Mala2/MouDio/Documentation/BT-806/Drivers/ReadMe.txt

CP210x.zip:
CP210x Windows Driver For BP109, DB101, DB102, DB005, DB006, etc
