Mala2/MouDio/Prototype/Old Version/README.md

# Bluetooth-Speaker
<p align="center">
**⚠  This project is currently still under development. If you came from Reddit just wait I will organize the files soon ⚠️**
	
Discord https://discord.gg/edw5AbDd
<p align="center">
     

</p>
<p align="center">
	<a href="https://github.com/Mala2/Bluetooth-Speaker/repo-size" alt="repo-size">
		</a>
	<a href="https://github.com/Mala2/Bluetooth-Speaker/issues" alt="Issues">
		</a>
	<a href="https://github.com/sparkfun/Qwiic_SerLCD_Py/blob/master/LICENSE" alt="License">
		</a> 
 	<a href="https://discord.gg/GqjnZJyF" alt="Issues">
		</a>
	<a href="https://twitter.com/intent/follow?screen_name=Electricshocksa">
        	</a>
	<a href="https://twitter.com/intent/follow?screen_name=Muhammadalali">
        	</a>
	<a href="https://github.com/Mala2">
        	</a>
	<a href="https://github.com/Mala2/Bluetooth-Speaker/stargazers" alt="stars">
		</a>

A fully function Bluetooth Speaker implement most of the new ICs chip.

The design consists of four PCBs (MAIN, USB-C, FRONT, TOP) and 3 microcontrollers. I build and test all the PCBs and they work as expected so the hardware design is done. **However, the software part is still under process.**

Please refer to the shared files for more information about specific PCB.

🎨 📐 FUSION 360 (https://a360.co/3uLzq06)

[*🎨 📐 View on FUSION 360*](https://a360.co/3uLzq06)

Features
-------------------
* **Amplifier** - The Texas Instruments® **TPA3130D2** Which has low distrition can output 2 × 15 W Into a 8-Ω BTL Load
* **Connectivity** - The [*FSC-BT806 Feasycom*](https://github.com/Mala2/FSC-BT806) features 
 Qualcomm® **CSR8675** - **Bluetooth V5.0** Support HSP, HFP, A2DP, AVRCP, PBAP,MAP,SPP,BLE profile - Coverage up to 15m - **True Wireless Stereo** to share BT audio stream between two Speakers - **Wired** analog input
* **Power** - Accept **USB PD** Delivery **5 to 24V** - **Fast Charging** in 3 hours - **USB A** Capable of **15W-5V,3A** - **Low idle power** consumption - A**10-hour** battery life - **5000mAh** battery capacity

* **Arduino IDE Programmable Bluetooth-Speaker**

Repository Contents
-------------------

👩‍🚀 **[.STL Files ](STL-Files)** • The **Bluetooth-Speaker** components in STL format (probably what you are looking for to 3d print)

🔉 **[Hardware](Hardware)** • The internal PCBs files (Gerber, Schematic) 

💻 **[Software](Software)** • Codes and Libraries for use with the **Bluetooth-Speaker**

📄 **[Documentation](Documentation)** • Data sheets, other references

🎥 **[Video](Video)** • Demonstration videos of the final project

🎲 **[Prototype](Prototype)** • Evaluation board, Cases, etc...

To Do List
-------------------

🔴 **Minimize the use of microcontrollers as the esp32 can handle much of the work done by atmegas.**
	
🔴 **Battery efficiency is critical here so using every possible way to reduce the consumption is needed.**
	
🔴 **The front PCB can only display time. I wanted to display weather temperature too with the help of ESP32.**
