Mala2/MouDio/Prototype/Old Version/Hardware/Main/README.md

<p align="center">
**⚠  This PCB is currently still under development. ⚠️**
  
FRONT
-------------------

FRONT (https://d2t1xqejof9utc.cloudfront.net/screenshots/pics/406df0fcc6033955165331e439d0659e/large.png)

BACK
-------------------

BACK (https://d2t1xqejof9utc.cloudfront.net/screenshots/pics/797c76d72846c0377390deae2d0703cb/large.png)
