Mala2/MouDio/Prototype/Old Version/Hardware/Laser Cut/README.md

You can use any Acrylic you would like, but in this case I wanted to hide the LEDs from direct view. The manfucture **Tap Plastics®** has a cool way to accomplish that by applying a unique Acrylic created for this reason.

By using the below **Chemcast Black LED Acrylic** all the LEDs will be hidden away inside and only let the light to glow through. In the other hand it will apear opaque once the LEDs are off

Chemcast Black LED Acrylic
--------------
Chemcast Black LED Acrylic (https://www.tapplastics.com/product/plastics/cut_to_size_plastic/black_led_sheet/668)

[*Chemcast Black LED Acrylic*](https://www.tapplastics.com/product/plastics/cut_to_size_plastic/black_led_sheet/668) **X1** For the front panel done by laser cut
