Mala2/MouDio/Prototype/Old Version/Hardware/Main/Schematic_Main_V1.pdf

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
H I | I J | J K | K 11 | 22 | 33 | 44 | 55 | 66 | 77 | 88 | 99

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
TITLE:
Sheet_1 | REV: 1.0
Date: | 2021-03-11

Sheet: 1/1
Drawn By: mfm1500

### Company: Your Company

16MHz

X1

TCEPQR

SW1

4

1

2
35

5v+ out

ATMEGA328P-AU

U11

(PCINT19/OC2B/INT1)PD3

1
(PCINT20/XCK/T0)PD4

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
(PCINT6/XTAL1/TOSC1)PB6

7
(PCINT7/XTAL2/TOSC2)PB7

8
(PCINT21/OC0B/T1)PD5

9
(PCINT22/OC0A/AIN0)PD6 10
(PCINT23/AIN1)PD7 11
(PCINT0/CLKO/ICP1)PB0 12
(PCINT1/OC1A)PB1 13
(PCINT2/SS#/OC1B)PB2 14
(PCINT3/OC2A/MOSI)PB3 15
(PCINT4/MISO)PB4 16 | PB5(SCK/PCINT5) 17 AVCC 18 ADC6 19 AREF 20 GND 21 ADC7 22 PC0(ADC0/PCINT8) 23 PC1(ADC1/PCINT9) 24 PC2(ADC2/PCINT10) 25 PC3(ADC3/PCINT11) 26 PC4(ADC4/SDA/PCINT12) 27 PC5(ADC5/SCL/PCINT13) 28 PC6(RESET#/PCINT14) 29 PD0(RXD/PCINT16) 30 PD1(TXD/PCINT17) 31 PD2(INT0/PCINT18) 32

A0_1

A1_1

A2_1

A3_1

A4_1

A5_1

RX_1

TX_1

D3_1 | D2_1
D4_1

D5_1
D6_1
D7_1
D8_1
D9_1
D10_1
D11_1
D12_1 | D13_1

22pF

C36

22pF

C37

## DTR_1 MICRO CONTROLLER

5v+ out | 5v+ out

## ATMEGA328

OUT_CH

LMBR120FT1G

D6

5v+ out

D11_1

GND

TX_1

RX_1
DTR_1

HDR-F-2.54_1x6

H2

1

2

3

4

5

6

5v+ out

rest_1

GND

GND

GND

100nF

C38

100nF

C39
100nF

C40 GND

GND

EN 5v

https://www.ti.com/tool/PMP9491

## VIN = 3V, VOUT = 12V,and IOUT = 2.5A

LM3481

## BOOST CONVERTER

https://www.ti.com/product/LM3481#design-development##all

LM3481MM/NOPB

U15

ISEN

1
UVLO

2
COMP

3
FB

4
AGND

5
FA/SYNC/SD

6

PGND

7

DR

8

VCC

9

VIN 10

470uF

C102
1uF

C103
1uF

C104

44.2k

XAL1010-332MEB

L10

1

2

MBRD835LT4G

D10

3

2

1

1uF

C105
1uF

C106

CSD16321Q5

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
R114

R115
100

3.32k

470nF

C112

## Vo=12V@2.5A

SJ

SJ7

2

1

GND

OUT_CH_1

GND

GND

GND

GND

GND

EN 12v

GND

Next time: you can use variable resistor controled with microcontrollers to set the gain "I2C protocol" https://www.ti.com/tool/PMP9491

RIN

LIN

4.7uF

C76

4.7uF

C77

RIN+

LIN+

4.7uF

C78
RIN-

LIN-

4.7uF

C79

TPA3130D2DAPR

U16

MODESEL

1
SDZ

2
FAULTZ

3
RINP

4
RINN

5
PLIMIT

6
GVDD

7
GAIN/SLV

8
GND

9
LINP 10
LINN 11
MUTE 12
AM2 13
AM1 14
AM0 15
SYNC 16 | AVCC 17 PVCC 18 PVCC 19 BSNL 20 OUTNL 21 GND 22 OUTPL 23 BSPL 24 GND 25 BSNR 26 OUTNR 27 GND 28 OUTPR 29 BSPR 30 PVCC 31 PVCC 32 EPAD ³³

PGND

SDZ

RIN+

LIN+

RIN-

LIN-

PLIM

R64
75K

47K

R63

1uF

C74

SGND

100K R61

SGND

4.7K

R62

47pF

C75

SGND

PGND | SGND

1000pF

C73
100nF

C71

PGND

BSNL

OUTNL

R69

10 PGND

10uH

L11

PGND
R68
3.32

PGND

J22
L-LN

R70
PGND

10uH

L12

PGND

R67

PGND

J21
L+
LP

OUTPL

BSPL

BSNR | PGND

R71

10uH

L13

PGND

R66

PGND

J20
R-RN

OUTNR

BSPR
OUTPR | PGND

R72

10

10

10

10uH

L14

PGND
PGND

R65

J19
R+
RP

1000pF

C72
100nF

C70

PGND

https://www.ti.com/product/TPA3130D2

## Amplifier TPA3130D2

3.32

3.32

3.32

GND

12V

D9_1

EN AMP

EN AMP

XH2.54-10P

J3

123456789

10

### XH2.54-10P

DATA_OUT

MUTE

MUTE

5V+

GND

OUT_CH

12V

5v+ out

A5_1 OUTLL

# GNDL

5V+

R

GND
5v+ out

OUTRR

1uF

C48
1uF

C43

A4_1

D7_1
D8_1

## SN74LVC1T45 LEVEL SHIFTER

GND

GND

100nF

C41

GND

100nF

C42

D5_1_LED_5V

SN74LVC1T45DBVT

U13

VCCA

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
VCCB

6

## SN74LVC1T45 LEVEL SHIFTER

GND

GND

100nF

C44

GND

100nF

C45

D6_1_LED_5V

SN74LVC1T45DBVT

U14

VCCA

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
VCCB

6

D5_1

D6_1

OUT_CH

OUT_CH | 5V+

5V+

D5_1_LED_5V
D6_1_LED_5V
LED+

A5_1
A4_1

HDR-F-2.54_1x2

H3 12

SDA

SCL

12V

Replace it with 10k as if digital used

LM5157

## Could be a good substitute for recent one

3.3 uH

R39 | 56.2K R40

2.2nF

C49
47nF

C50

R41

R42
56.2k

10pF

C51

R43
0.004

STAT

8.45K

R47

5V

RX_1
A3_1

5v+ out R L

GND-sound

A2541WR-7P

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
STAT

OUT_CH

DATA_OUT

5V

GND

OUT_CH

A2541WR-7P

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
TPS61235PRWLT

U1

PGND

1
SW

2
VIN

3
CC

4
AGND

5

FB

6

EN

7

INACT

8

VOUT

9

OUT_CH

GND
GND

GND

100nF

C21

GND

1M

R12
100nF

C24
34K

R13

## Boost Converter 5V 2A

22uF

C17

22uF

C18
22uF

C19
22uF
EN 5v | C20

1M

R1

332K
R2

5V+

D4_1 | EN BLE

FSC-BT806

IC1

GND_1

1

AIO0

2

AIO1

3

I2S_CLK

4

I2S_IN

5

I2S_OUT

6

I2S_WS

7

RESET

8

SPI_CSB

9

SPI_MOSI

10

SPI_MISO

11

SPI_CLK

12

BT_TX

13

BT_RX

14

BT_CTS

15

BT_RTS

16

LED0

17

LED1

18

LED2

19

PIO0

20

PIO1

21

GND_2

22

PIO2

23

PIO3

24

PIO4

25

PIO5

26

PIO6

27

PIO7

28

PIO14

29

PIO15

30

VDD_USB/3.3V_OUT

31

GND_3

32

VBAT_IN

33

VREGENABLE

34

1.8V_OUT

35

VDD_IO

36

USB_DP

37

USB_DN

38

VCC_CHG

39

MIC_RP

40

MIC_RN

41

MIC_R_BIAS

42

MIC_LP

43

MIC_LN

44

MIC_L_BIAS

45

SPK_RN

46

SPK_RP

47

SPK_LN

48

SPK_LP

49

GND_4

50

EXT_ANT

51

GND_5

52

GMI3015P-2C66DB

# MIC1¹²

GMI3015P-2C66DB

# MIC2¹²

MIC_L | MIC_R 15nH

L1
15nH

L2

15pF

C2
15pF

C3

GND_F | GND_F
GND_F | GND_F 100nF

C4
100nF

C5

100nF

C6
100nF

C7

2.2K

R6
2.2K

R7

MIC_RP

MIC_RN

MIC_L_P

MIC_L_N

MIC_BIAS_A | MIC_BIAS_B 0
MIC | R11

MIC/LINE_RN

MIC/LINE_RP

MIC/LINE_LN

MIC/LINE_LP

GND_F

SPK_L_P

SPK_L_N

SPK_R_P

SPK_R_N

MIC_BIAS_A

MIC/LINE_LN

MIC/LINE_LP

MIC_BIAS_B

MIC/LINE_RN

MIC/LINE_RP

USB_5V

1uF

C8

GND_F

3V3_MAIN

0

R15

1V8

0

R16

1uF

C9

GND_F

# VREG_IN³V³_MAIN

100nF

C10

4.7uF

C11

# GND_F ⁰

R17

2.2uF

C12

PIO15

PIO14

PIO7

PIO6

PIO5

PIO4

PIO3

PIO2

GND_F

PIO1

PIO0

LED2

LED1

LED0

BT_RTS

BT_CTS

BT_RX

BT_TX

SPI_CLK

SPI_MISO

SPI_MOSI

SPI_CSB

RESET

PCM-SYNC

PCM-OUT

PCM-IN

PCM-CLK

AIO1

AIO0

GND_F

BL9198-33BAPRN

U3

VIN

1
GND

2
EN
3 | NC

4

VOUT

5 | 3V3_MAIN

GND_F

100nF

C14
10pF

C15

GND_F

VBAT

## 3V3 regulator

NC

NC

NC

RESET

3V3_MAIN

100nF

C27

GND_F

3V3_MAIN

BT_RTS

NC

15K

R50

GND_F

100nF

C28

HDR-M-2.54_1x1

MUTE 1

## EN Pin(MUTE)

HDR-M-2.54_1x4

J1

k1
K2
K3
COM

VREG_IN

GND_F

POWER/PLAY/PAUSE
VOL+/NEXT
VOL-/BACK

K1: Long press for 2 seconds to Power On, short press to Pause K2: Long press to Volume+, short press to switch to Next Song K3: Long press to Volume-, short press to switch to Last Song

## Push Buttons

FC-B1010RGBT-HG

LED4

234

LED0

LED1
3V3_MAIN | LED2

## LED Indication

3V3_MAIN

PIO6
PIO7

## FSC-BT806B (CSR8675)

J4SD

J5
EN

EN: HIGH = ON

SD: LOW = ON

SDZ: HIGH = ON

PGND= POWER GND
SGND= SIGNAL GND
YOU SHOULD SEPARATE THEM NEAR THE DEVICE

XH2.54-4P

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
3V3_MAIN

LED11

LED22

LED00

LED11
LED22
LED00

Touch pad copy

D2

1

Touch pad copy

D3

1

Touch pad copy

A1

1

Touch pad copy

A0

1

A1_1

A0_1

## ATMEGA328 (Pinout)

12V

## (TPS61235P)

Jumper

JP2

GND

D2_1

D3_1

GND GND_F

JP4 Jumper

HDR-M-2.54_1x4

J7123

SPK_L_P

4

SPK_L_N

SPK_R_P

SPK_R_N

VBAT | OUT_CH

Touch pad copy

D4

1 D4_1

5017

U61 1

5017

U71 1

5017

1

U9

1

HDR-M-2.54_1x1

CH_B1 1

HDR-M-2.54_1x1

CH_A1
1

OUT_CH

MP3432

## 30W Boost Converter, VIN=2.7V

U10
1uH

L1

100uF

C34

C=0.22uF

2 | 15 W Into a 8- BTL Load at 15 V
Should be 10uF | https://ohmslawcalculator.com/voltage-divider-calculator
| DS1841

DS1841N+

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
RGND

6

RW

7

RH

8

NC

9

SCL 10

EP 11

OUT_CH_1
GND

OUT_CH

EN 12v

Touch pad copy

EN21

## AUDIO OUTPUT

SPK_R_N

SPK_L_N

SPK_R_P

SPK_L_P

MAX16054AZT+T

U2

IN

1
GND

2
CLEAR
3 | #OUT

4

OUT

5

VCC

6

## On/Off Controller MAX16054

5017

RN1 1

5017

LN

1 1

5017

1

RP

1

5017

LP

1 1

5.23K

R18

5.23K

R19

A5_1

A4_1

5v+ out

5v+ out

A5_1
A4_1

5v+ out

GND | 100nF C23

# GND RH

Jumper

JP1

RH

Touch pad copy

SDZ

1

D10_1

GND

IN
OUT_CH

Touch pad copy

O+

1

Touch pad copy

O-

1

O+
O-

O+

O-

HDR-F-2.54_1x2

H512

IN
GND

C0805X106J9RACTU

GMI6027P-2C-52db

MIC3

12

100nF

C26

1M

R14

1M

R20 | MAX4466 U4

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
10uF

C29

20K

R22
TC33X-2-104E

R23

100pF

C30

NFZ2MSM301SN10L

FB1

1

1
2

2

NFZ2MSM301SN10L

FB2

1

1
2

2

GND

5v+ out | 5v+ f

gnd f

gnd f
gnd f

gnd f

gnd f

5v+ f

5v+ f

5v+ f

out_AMP

220
R24

OUTRR

OUTLL

gnd f

270uF

C46
270uF

C47

MIC94041YFL-TR

U5

VOUT

1
GND

2
VIN

3

EN

4 EN 12v

2SK3541T2L

Q1

GND_F

1uF

C32 | VREG_IN

3V3_MAIN

HDR-F-2.54_1x2

H612

3V3_MAIN

GND_F

HDR-F-2.54_1x2

H712

OUT_CH

GND

HDR-F-2.54_1x2

H812

BT_TX
BT_RX

HDR-M-2.54_1x1

CH_B2 1

HDR-M-2.54_1x1

CH_B3 1

HDR-M-2.54_1x1

CH_B4 1

GND

GND

GND

GND

## Polypropylene (PP) film capacitors are best for audio

## AUDIO DETECTOR

Mouser Part #
80-R71XN447050H0K

Mouser Part #
80-R71XN447050H0K

80-R71XR510050H0K

OR

TPA3129D2 is better AMP

https://www.ti.com/lit/an/sloa201/sloa201.pdf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

LC FILTER

RC SNUBBER

You may need to add I2C breakout

667-ECW-FD2W475JB

OR

10nF

C52

OR
MKP2G021001C00JI00

Mouser Part #
GRM21BR72A103KA01L
C97925

10nF

C53

10nF

C55

10nF

C56

0.68uF

C57

Mouser Part #
GRM31MR71H684KA88L

ECW-F2684HAB

OR

0.68uF

C58

0.68uF

C59

0.68uF

C60

OR
MKP2F032201K00JSSD

Mouser Part #
810-C1608X7R1H224K

0.22uF

C61

0.22uF
C62

0.22uF

C63

0.22uF
C64

PGND

Mouser Part #
GRM1885C1H331JA01D

FKP2D003301D00JA00

OR

C85978

330pF

C65

330pF

C66

330pF

C67

330pF

C68

100uF

C1

100uF

C33
100uF

C16

200485-0710

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
GND_1

G1

GND_2

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
## TPS22969

## USE INSTEAD

TPS22969DNYT

U12

VIN_1

1

VIN_2

2

VBIAS

3

ON

4
GND

5

VOUT_1

6

VOUT_2

7

VOUT_3

8

VIN_3

9

## TPS22990

TPS22990

U17

CT

1
NC

2
VIN

3
VBIAS

4
ON
5 | GND

6

PG

7

VOUT

8

VOUT

9

VOUT

10

100K

R32 100K R33

100K

R25

100K

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
100K

R48

100K

R46

1K

R49

100uF

C22
100uF

C25

whiteLEDSMD

LED1

220
R28

220
R29

4.7uF

C13

270uF

C35

Mouser Part #
CLF12577NIT-100M-D

OR

1D23A-100M

SER2915L-332KL

U18

2

2
1

1
