Mala2/MouDio/Documentation/Pics/back 1.png

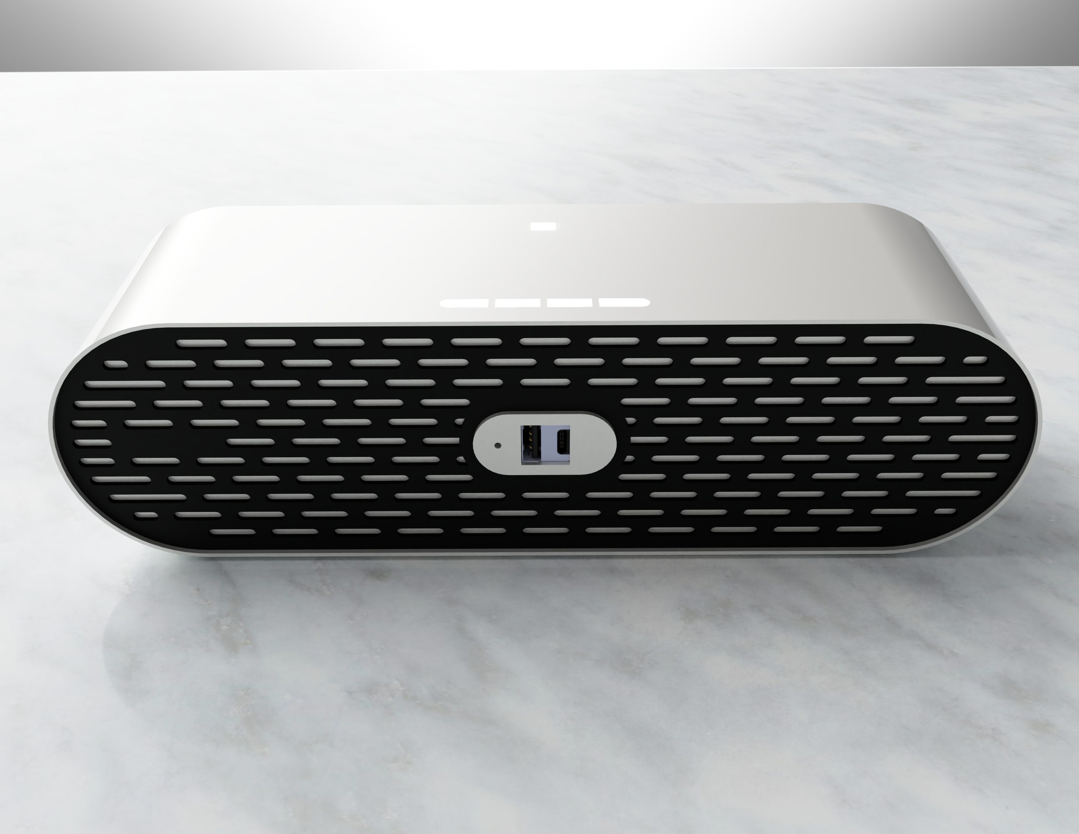
Documentation/Pics/back 1.png
