Mala2/MouDio/Documentation/Pics/back.png

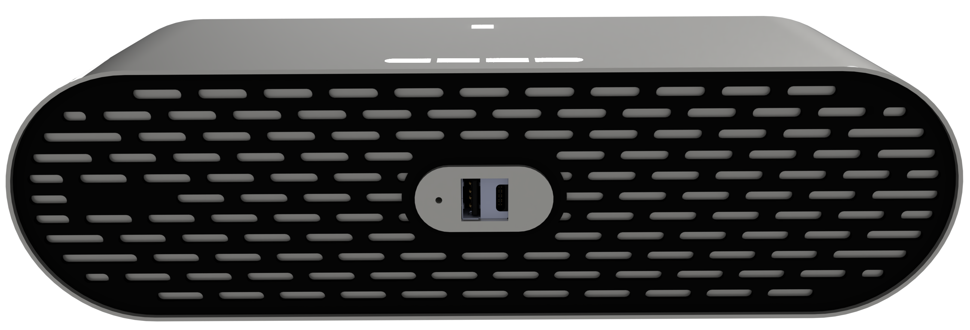
Documentation/Pics/back.png
