Mala2/MouDio/Documentation/Pics/BACK_Charger.png

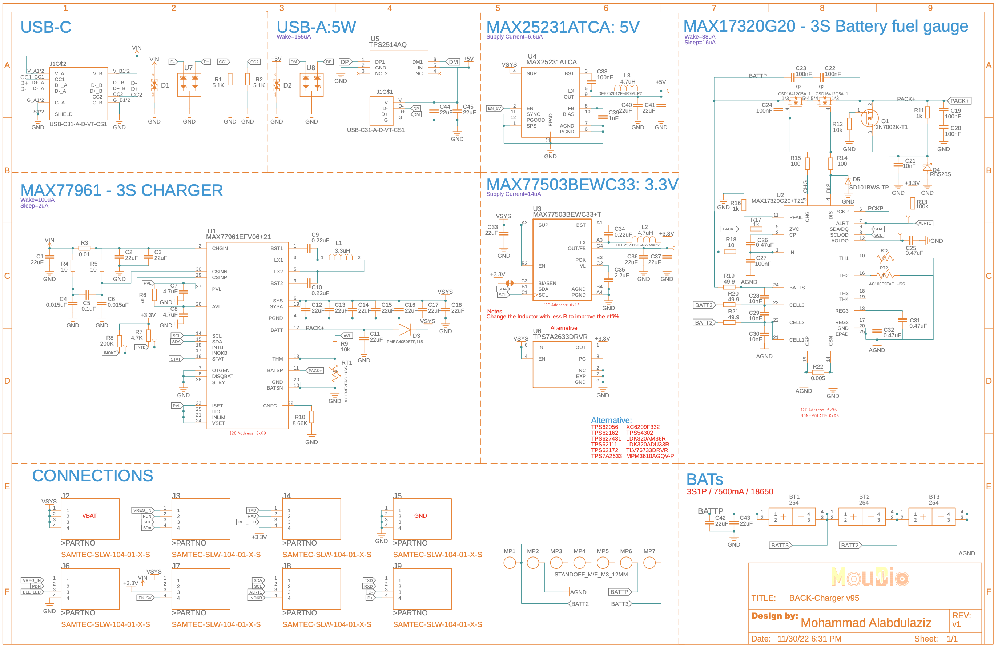
Documentation/Pics/BACK_Charger.png
