Mala2/MouDio/Documentation/Pics/BACK_Chargere_T.png

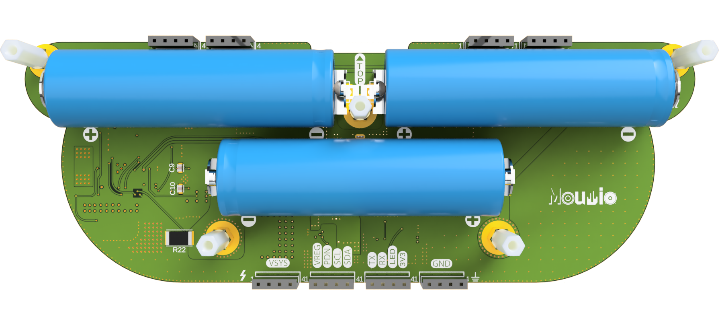
Documentation/Pics/BACK_Chargere_T.png
