Mala2/MouDio/Documentation/Pics/Battery Extension PCB Back V2.png

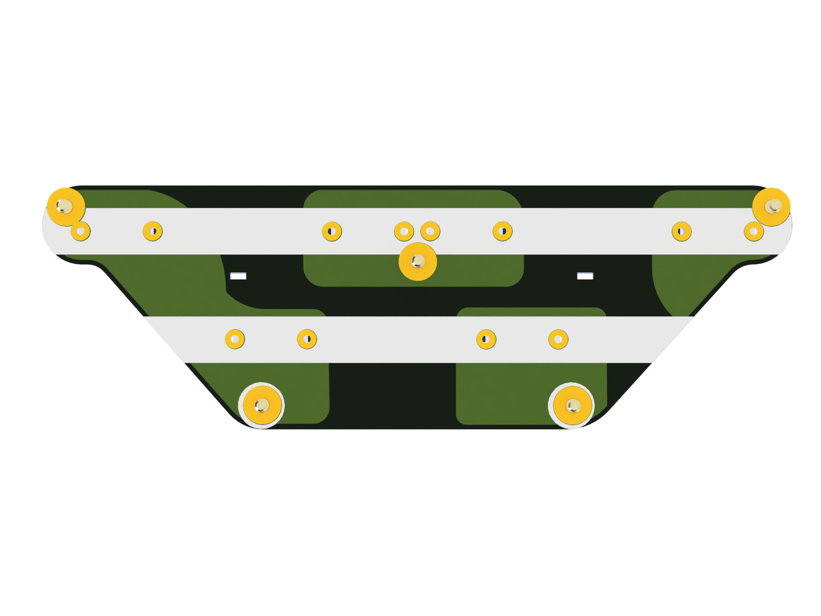
Documentation/Pics/Battery Extension PCB Back V2.png
