Mala2/MouDio/Documentation/Pics/Battery Extension PCB Front V2.png

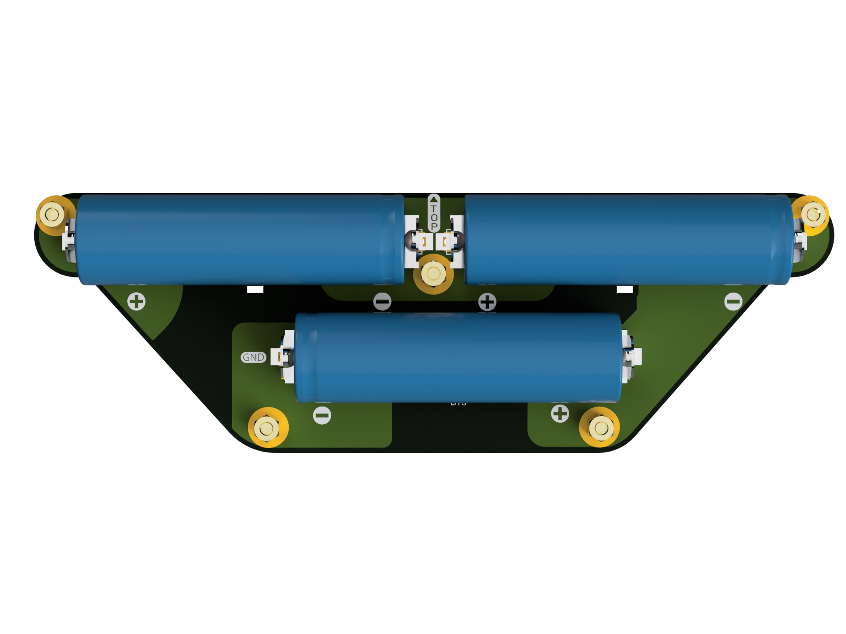
Documentation/Pics/Battery Extension PCB Front V2.png
