Mala2/MouDio/Documentation/Pics/BLUETOOTH SPEAKER 1.png

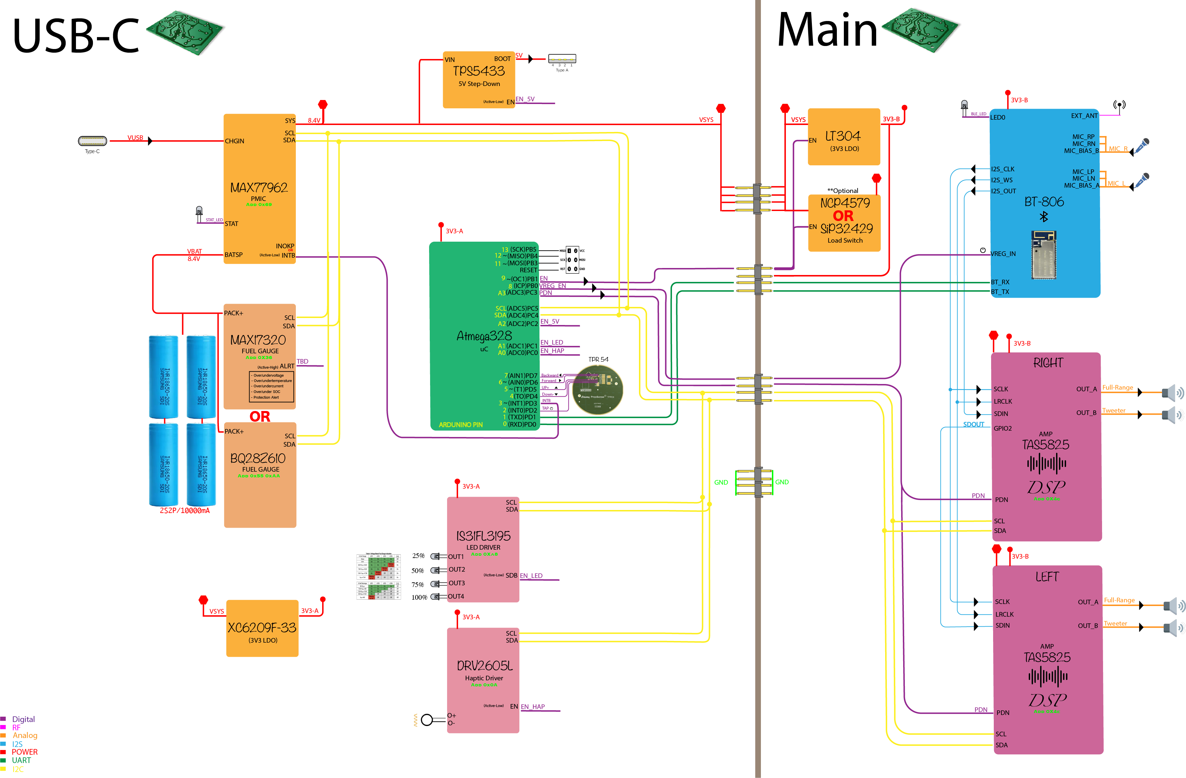
Documentation/Pics/BLUETOOTH SPEAKER 1.png
