Mala2/MouDio/Documentation/Pics/BOTTOM_Amplifier.png

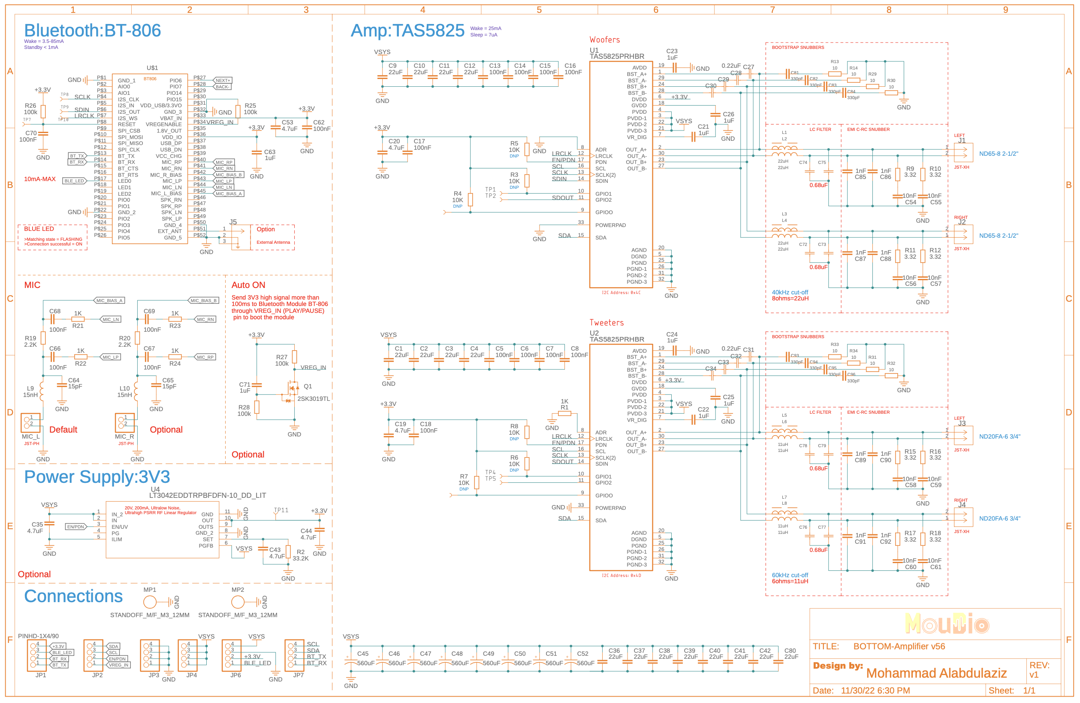
Documentation/Pics/BOTTOM_Amplifier.png
