Mala2/MouDio/Documentation/Pics/BOTTOM_Amplifier_B.png

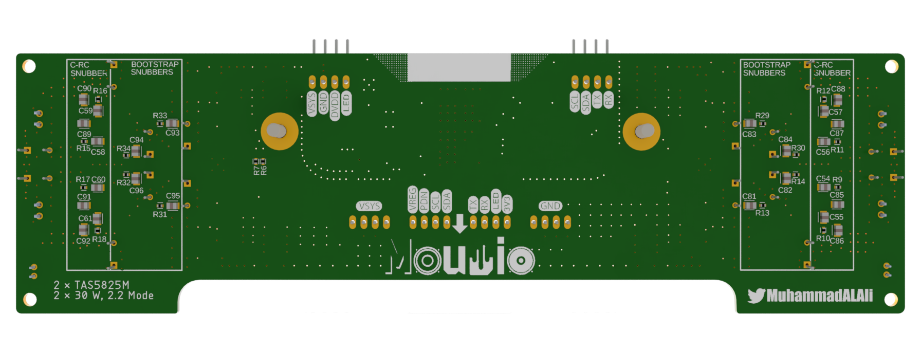
Documentation/Pics/BOTTOM_Amplifier_B.png
