Mala2/MouDio/Documentation/Pics/BOTTOM_Amplifier_T.png

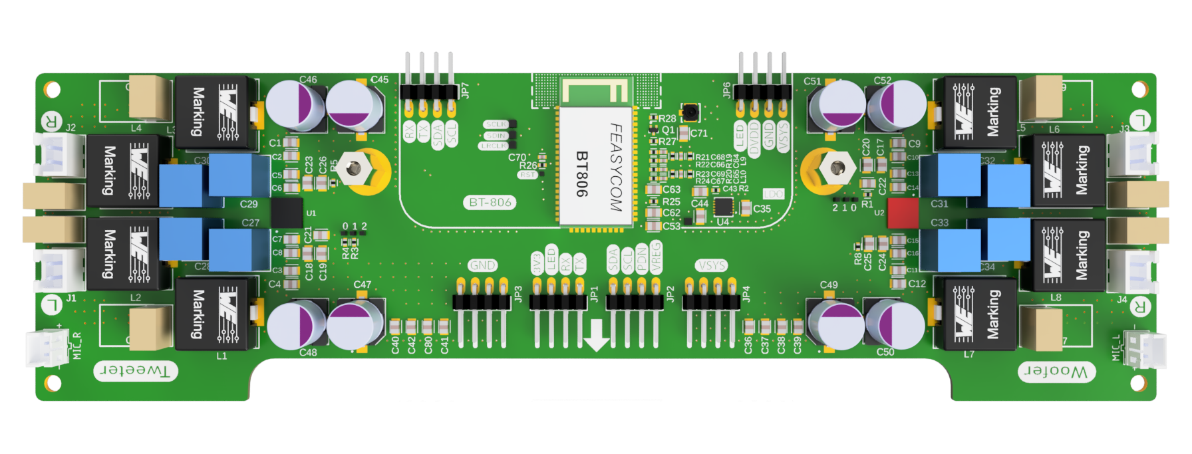
Documentation/Pics/BOTTOM_Amplifier_T.png
