Mala2/MouDio/Documentation/Pics/front angle.png

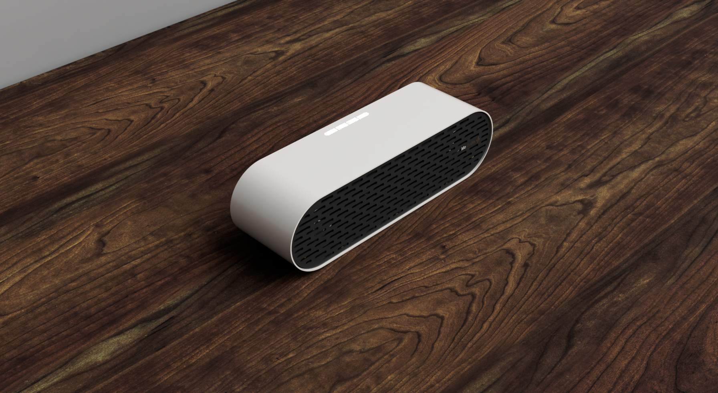
Documentation/Pics/front angle.png
