Mala2/MouDio/Documentation/Pics/front black.png

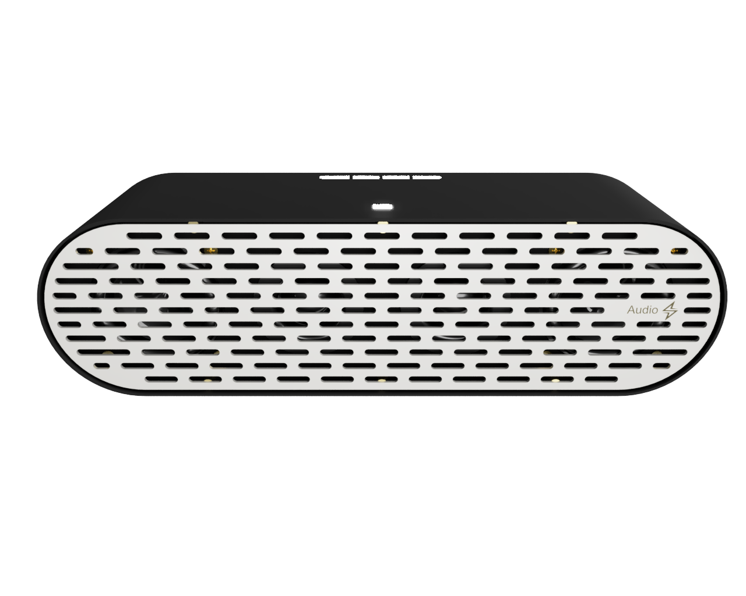
Documentation/Pics/front black.png
