Mala2/MouDio/Documentation/Pics/front cer.png

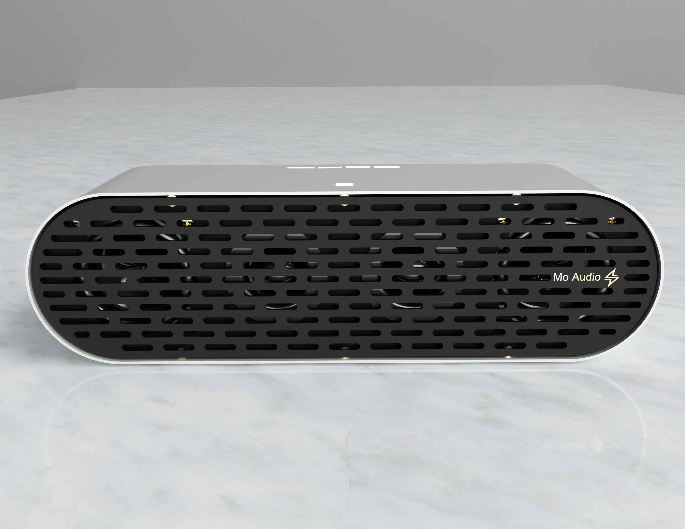
Documentation/Pics/front cer.png
