Mala2/MouDio/Documentation/Pics/front oreg.png

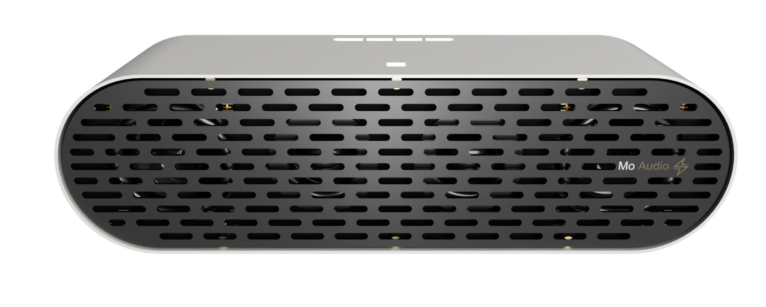
Documentation/Pics/front oreg.png
