Mala2/MouDio/Documentation/Pics/front wood.png

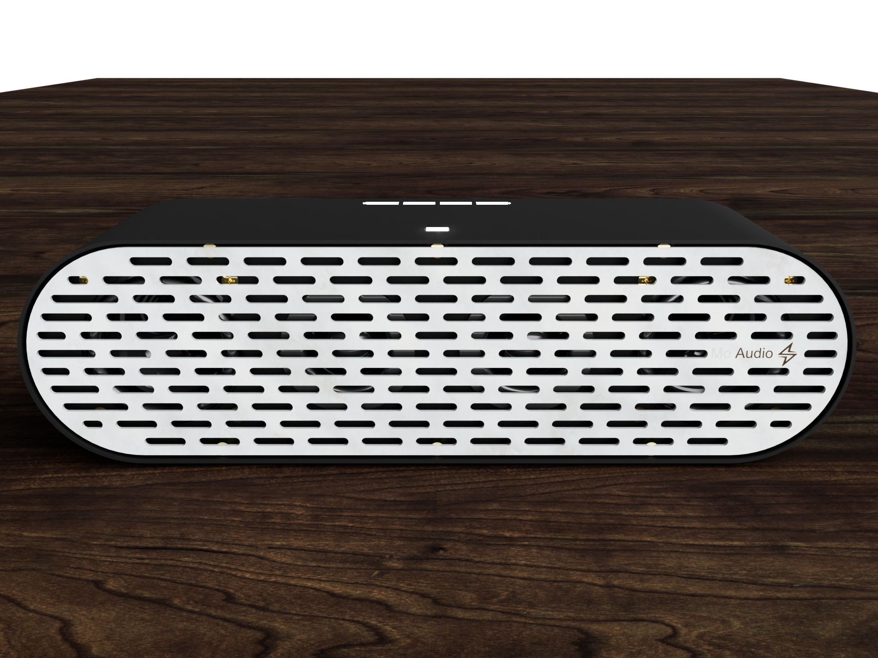
Documentation/Pics/front wood.png
