Mala2/MouDio/Documentation/Pics/front.png

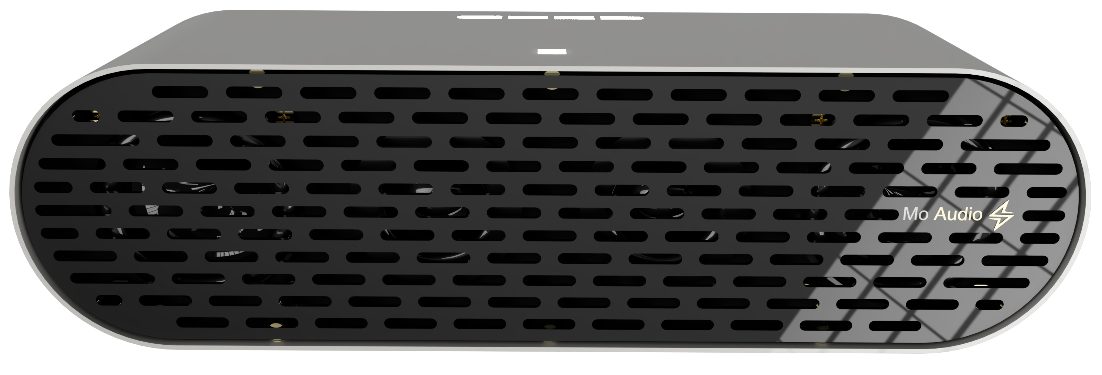
Documentation/Pics/front.png
