Mala2/MouDio/Documentation/Pics/FRONT_Speaker.png

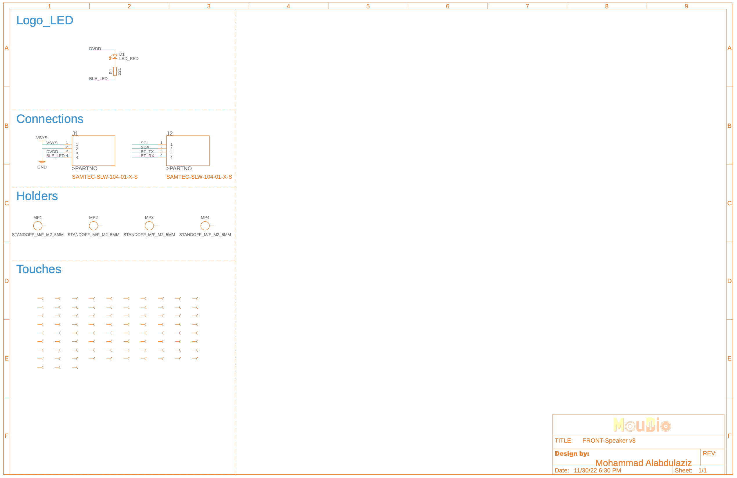
Documentation/Pics/FRONT_Speaker.png
