Mala2/MouDio/Documentation/Pics/Front_Speaker_B.png

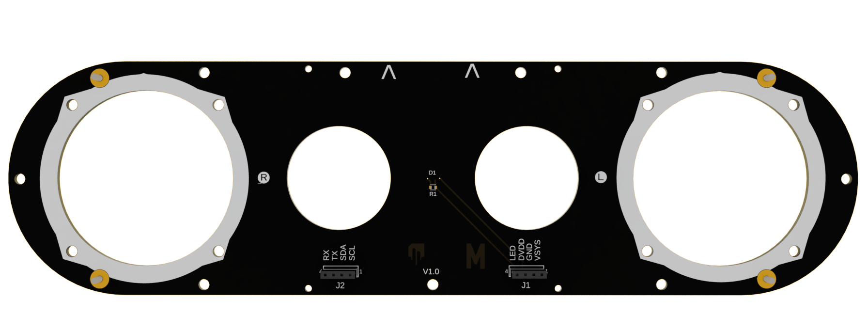
Documentation/Pics/Front_Speaker_B.png
