Mala2/MouDio/Documentation/Pics/FRONT_Speaker_T.png

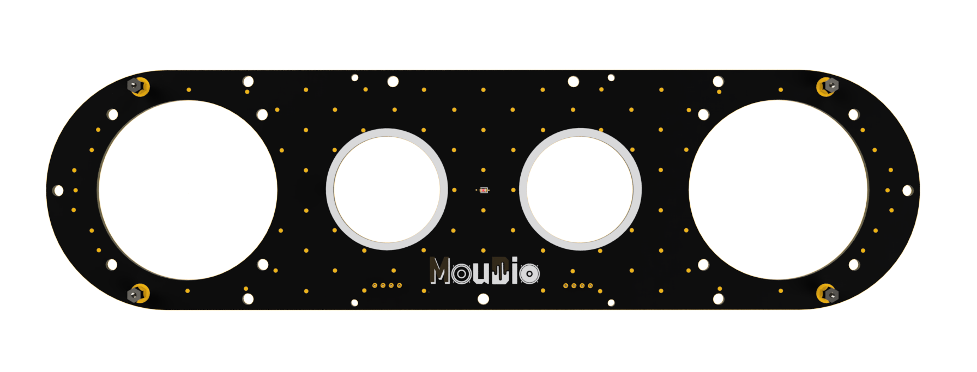
Documentation/Pics/FRONT_Speaker_T.png
