Mala2/MouDio/Documentation/Pics/frotnangle 2.png

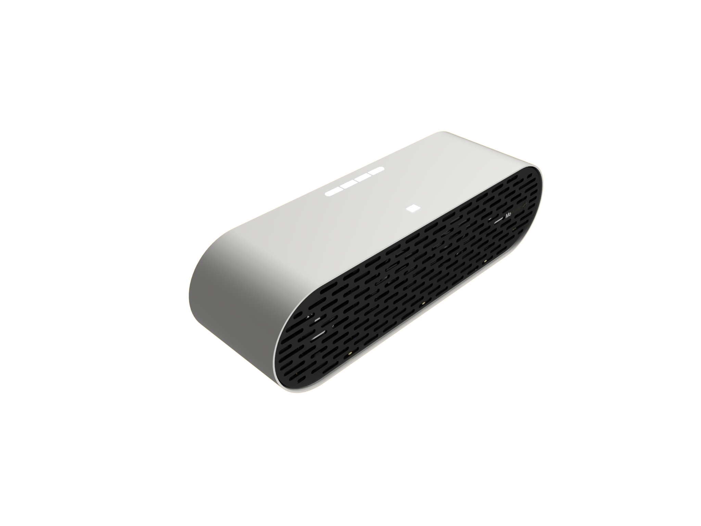
Documentation/Pics/frotnangle 2.png
