Mala2/MouDio/Documentation/Pics/MASHA.png

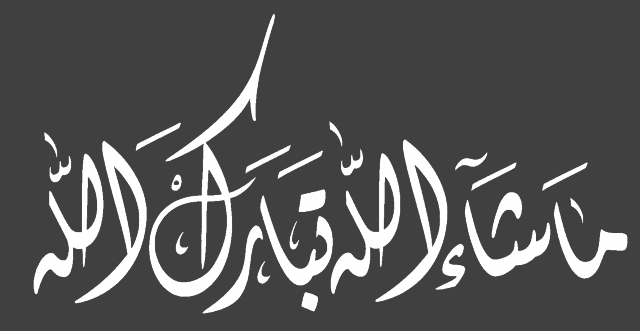
Documentation/Pics/MASHA.png
