Mala2/MouDio/Documentation/Pics/SPK1.png

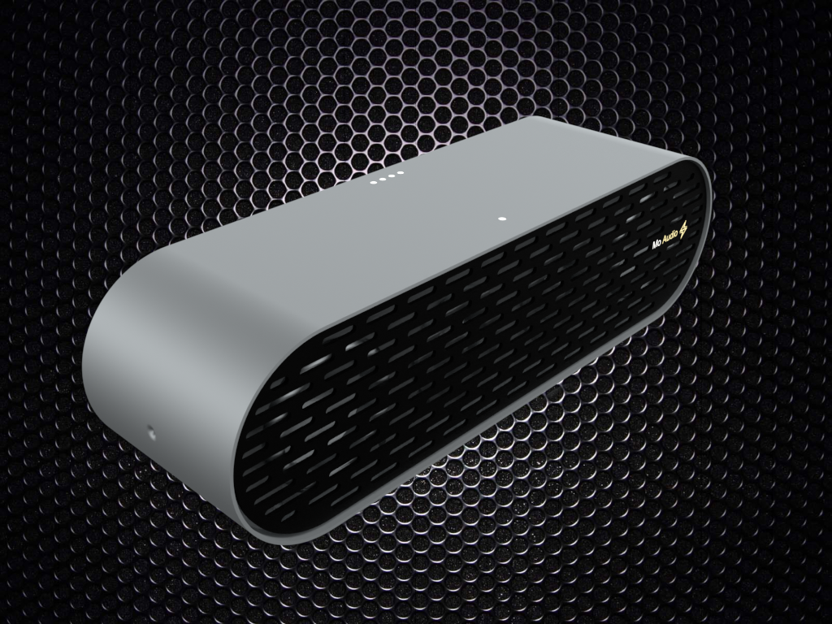
Documentation/Pics/SPK1.png
