Mala2/MouDio/Documentation/Pics/TOP_Main.png

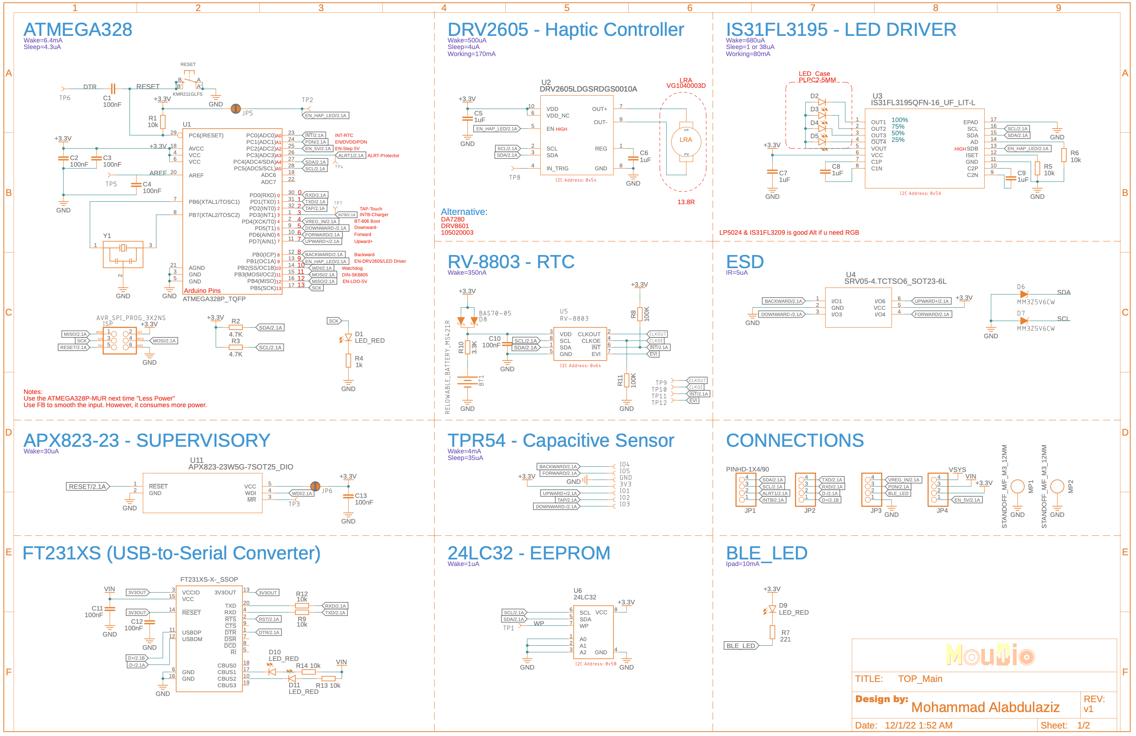
Documentation/Pics/TOP_Main.png
