Mala2/MouDio/Documentation/Pics/TOP_Main_B.png

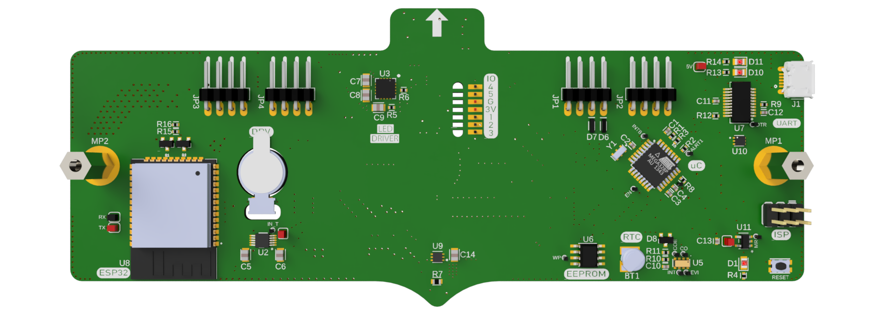
Documentation/Pics/TOP_Main_B.png
