Mala2/MouDio/Documentation/Pics/TOP_Main_T.png

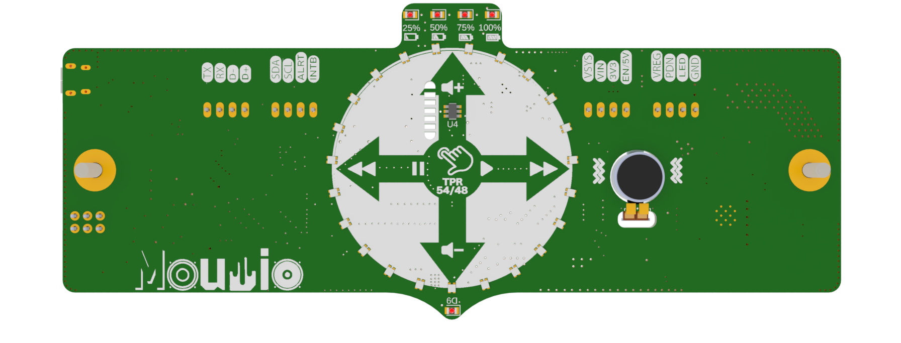
Documentation/Pics/TOP_Main_T.png
