Mala2/MouDio/Hardware/FRONT/FRONT_Speaker.xlsx

Country of Origin may be different at time of shipment.
The HTSUS and ECCN information shown is for informational purposes only and is not a representation or warranty as to the accuracy or reliability of these classifications. All information is provided "as is" and is subject to change without notice. Any use made of the information provided is without recourse to Digi-Key and at the user's risk.
Index | Manufacturer Part Number | Manufacturer Name | Description | Availability | Stock Status | Attrition % | Requested Quantity 1 | Pack Quantity 1 | Pack Type 1 | Digi-Key Part Number 1 | Unit Price 1 | Extended Price 1 | Minimum Order Quantity 1 | Customer Reference | Requested Part Number | Lead Weeks | Datasheet | Reference Designator | US Import Tariff | Note | Part Status | RoHS Status | ECCN | HTSUS | Country of Origin | Environmental Information | Original Part numbers | Image
1 | QBLP631-IW | QT Brightek (QTB) | LED WHITE DIFFUSED 0805 SMD | 107,567 | In Stock |  | 1 | 1 | Cut Tape (CT) | 1516-1085-1-ND | 0.45000 | $0.45 | 1 |  | QBLP631-IW | 1 | https://www.qt-brightek.com/datasheet/QBLP631_series.pdf | D1 | N/A |  | Active | ROHS3 Compliant | EAR99 | 8541.41.0000 | China | https://media.digikey.com/pdf/Compliance/QT%20Brightek/RoHS2_Declaration_of_Conformity.pdf | QBLP631-IW | https://media.digikey.com/Photos/QT%20Brightek%20Photos/MFG_QBLP631-IW.jpg
2 | RC0402FR-07221RL | YAGEO | RES 221 OHM 1% 1/16W 0402 | 4,805,495 | In Stock |  | 1 | 1 | Cut Tape (CT) | 311-221LRCT-ND | 0.10000 | $0.10 | 1 |  | RC0402FR-07221RL | 20 | https://www.yageo.com/upload/media/product/productsearch/datasheet/rchip/PYu-RC_Group_51_RoHS_L_12.pdf | R1 | N/A |  | Active | ROHS3 Compliant | EAR99 | 8533.21.0030 | Taiwan | https://www.yageo.com/en/Download/Index/certificates#rchip | RC0402FR-07221RL | https://media.digikey.com/Renders/Yageo%20Renders/0402-(1005-Metric).jpg
3 | SSW-104-01-T-S | Samtec Inc. | CONN RCPT 4POS 0.1 TIN PCB | 1,473 | In Stock - Value Added |  | 2 | 2 | Bulk | SAM1213-04-ND | 0.73000 | $1.46 | 1 |  | SSW-104-01-T-S | 2 | http://suddendocs.samtec.com/catalog_english/ssw_th.pdf | J1,J2 | N/A |  | Active | ROHS3 Compliant | EAR99 | 8536.69.4040 | Vietnam |  | SSW-104-01-T-S | https://media.digikey.com/Renders/Samtec%20Renders/SSW-104-x1-T-S.jpg
4 | 971050244 | Würth Elektronik | BRASS SPACER STUD METRIC THREAD | 8,932 | In Stock |  | 4 | 4 | Bulk | 732-12897-ND | 0.66000 | $2.64 | 1 |  | 971050244 | 26 | https://katalog.we-online.com/em/datasheet/971050244.pdf | MP1,MP2,MP3,MP4 | N/A |  | Active | ROHS3 Compliant | EAR99 | 7419.80.5050 | Germany |  | 971050244 | https://media.digikey.com/Photos/Wurth%20Electronics%20Photos/971050244.jpg
