Mala2/MouDio/Documentation/Pics/Body print.png

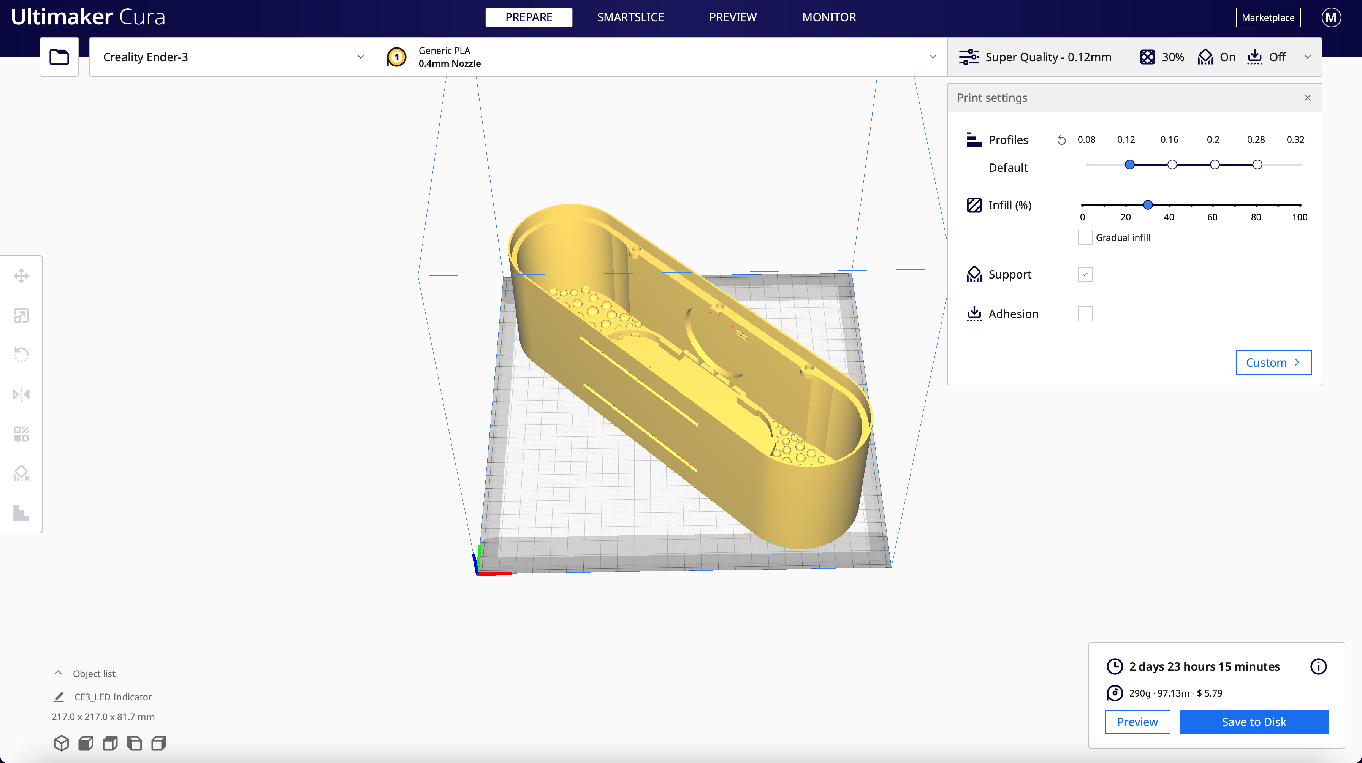
Documentation/Pics/Body print.png
