Mala2/MouDio/Prototype/STL-Files/Sealed Woofer + Twrt Speaker Test/README.md

This is a sealed enclosure to test the Dayton Audio ND65-8 2-1/2" Aluminum Cone Full-Range Neo Driver 8 Ohm or 4 Ohm and the Dayton Audio ND20FA-6 3/4" Soft Dome Neodymium Tweeter
