Mala2/MouDio/Prototype/STL-Files/Sealed Woofer Speaker Test/speaker test Drawing v5.pdf

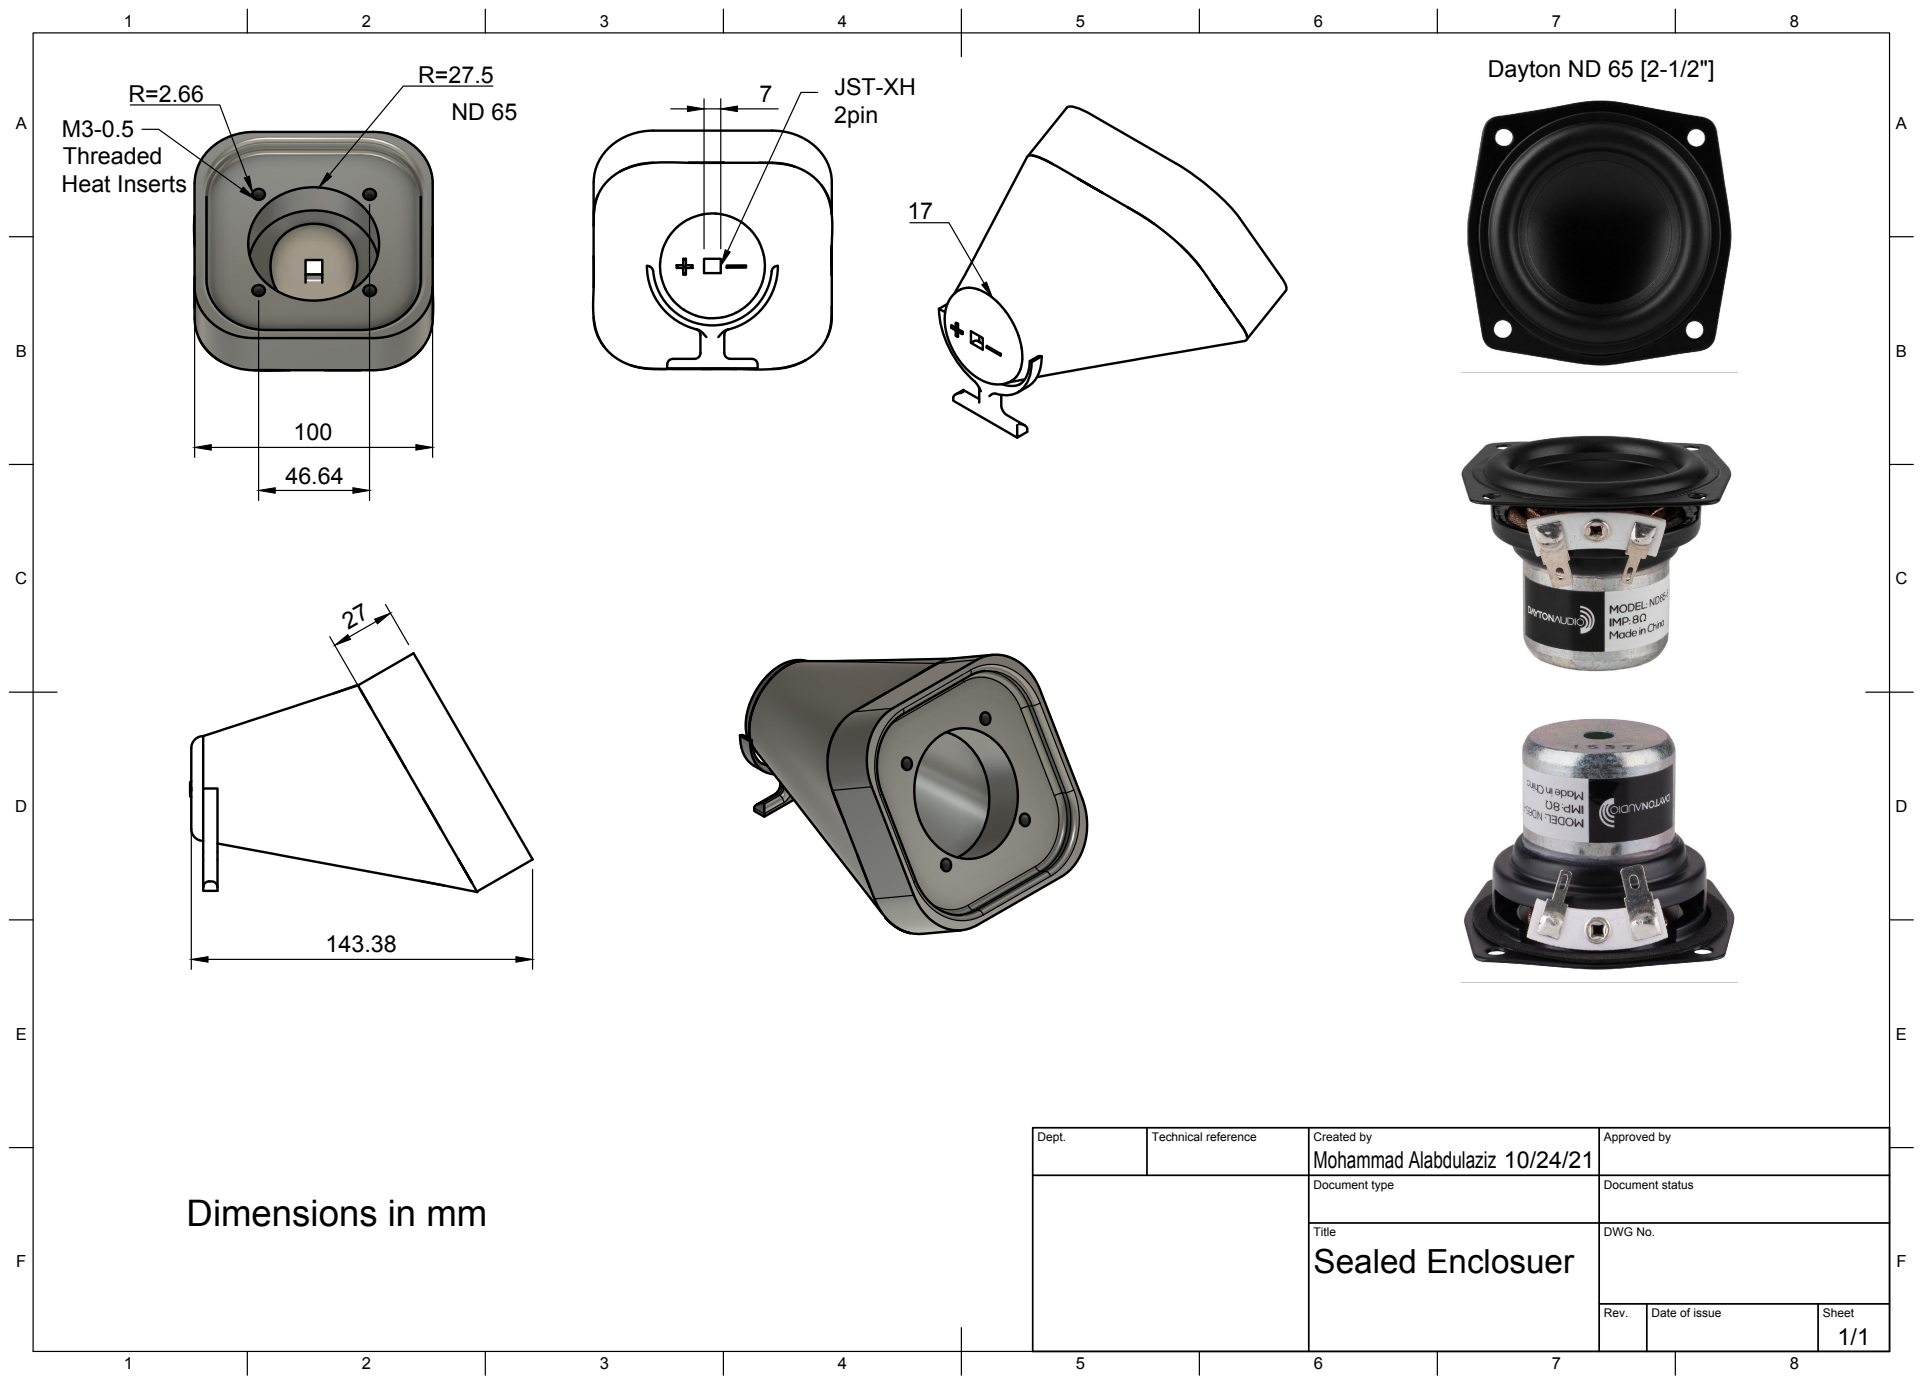
[picture p53: page 1]
Title; DWG No.; Rev.; Date of issue; Sheet; Sealed Enclosuer; Dayton ND 65 [2-1/2"]; Heat Inserts

Dept. | Technical reference | Created by Mohammad Alabdulaziz 10/24/21 | Approved by

Document type | Document status

Dimensions in mm
