Mala2/MouDio/3D-Files/Moudio Drawing.pdf

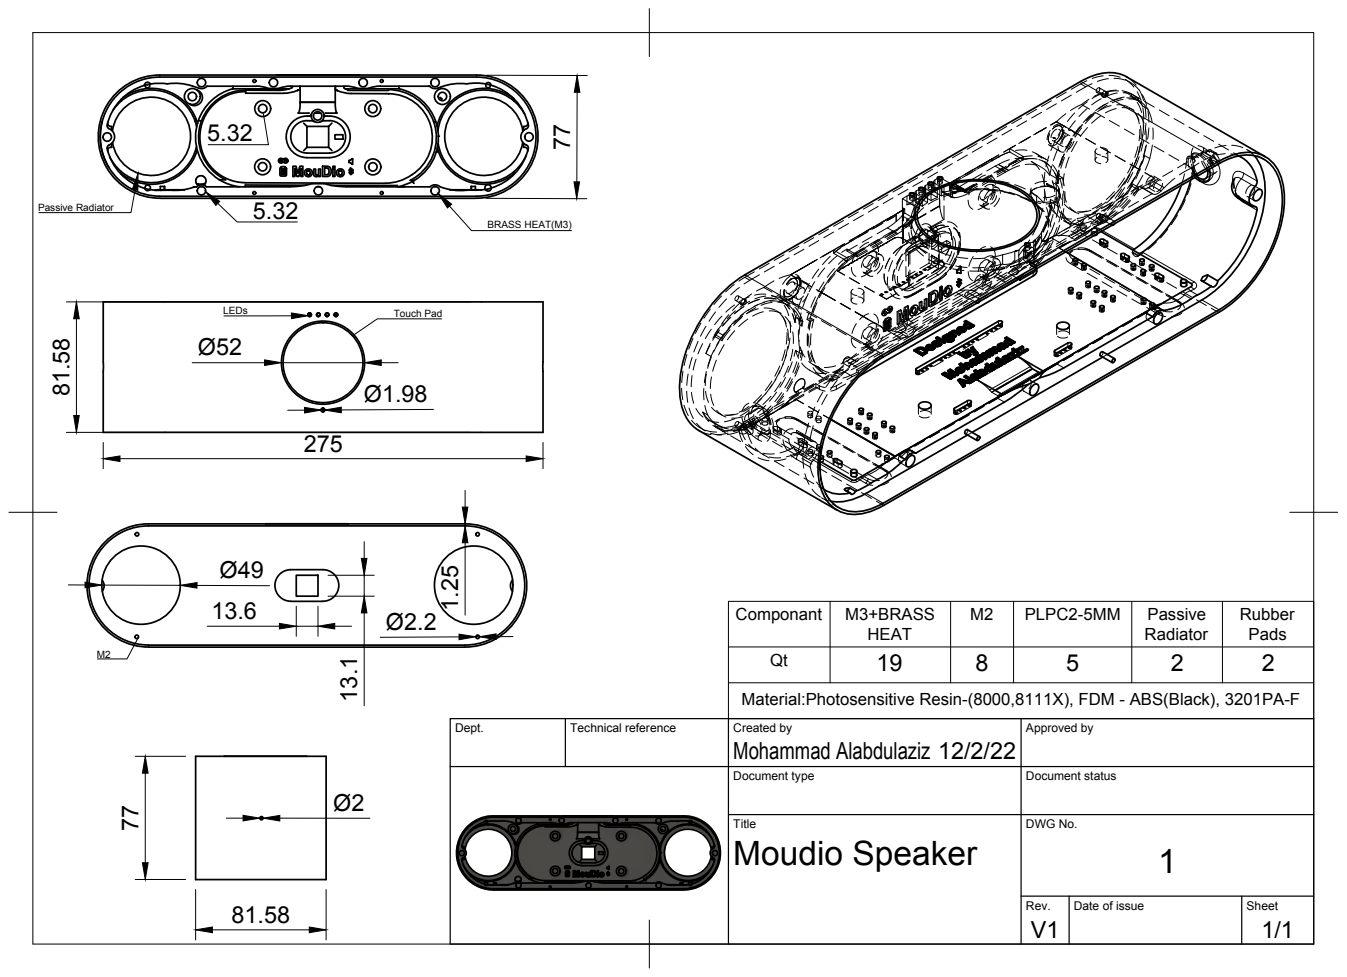
[picture p54: page 1]
Dept.; Technical reference; Created by; Approved by; Document type; Document status; Title; DWG No.; Rev.; Date of issue; Sheet; Moudio Speaker; Mohammad Alabdulaziz; Touch Pad LEDs

BRASS HEAT(M3) Passive Radiator

Material:Photosensitive Resin-(8000,8111X), FDM - ABS(Black), 3201PA-F
