Mala2/MouDio/3D-Files/Grill/Front Grill Drawing.pdf

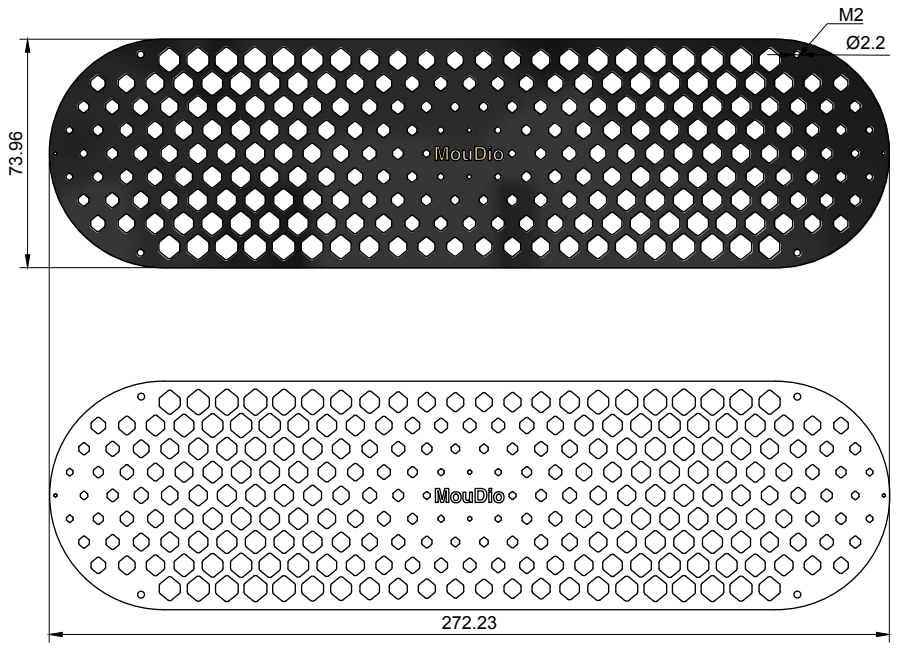
[picture p57: page 1]
