Mala2/MouDio/Prototype/Old Version/Video/Schematic_Speaker v4.pdf

3V LDO Regulator | Fuel gauge_LC709203

## Battery Charger

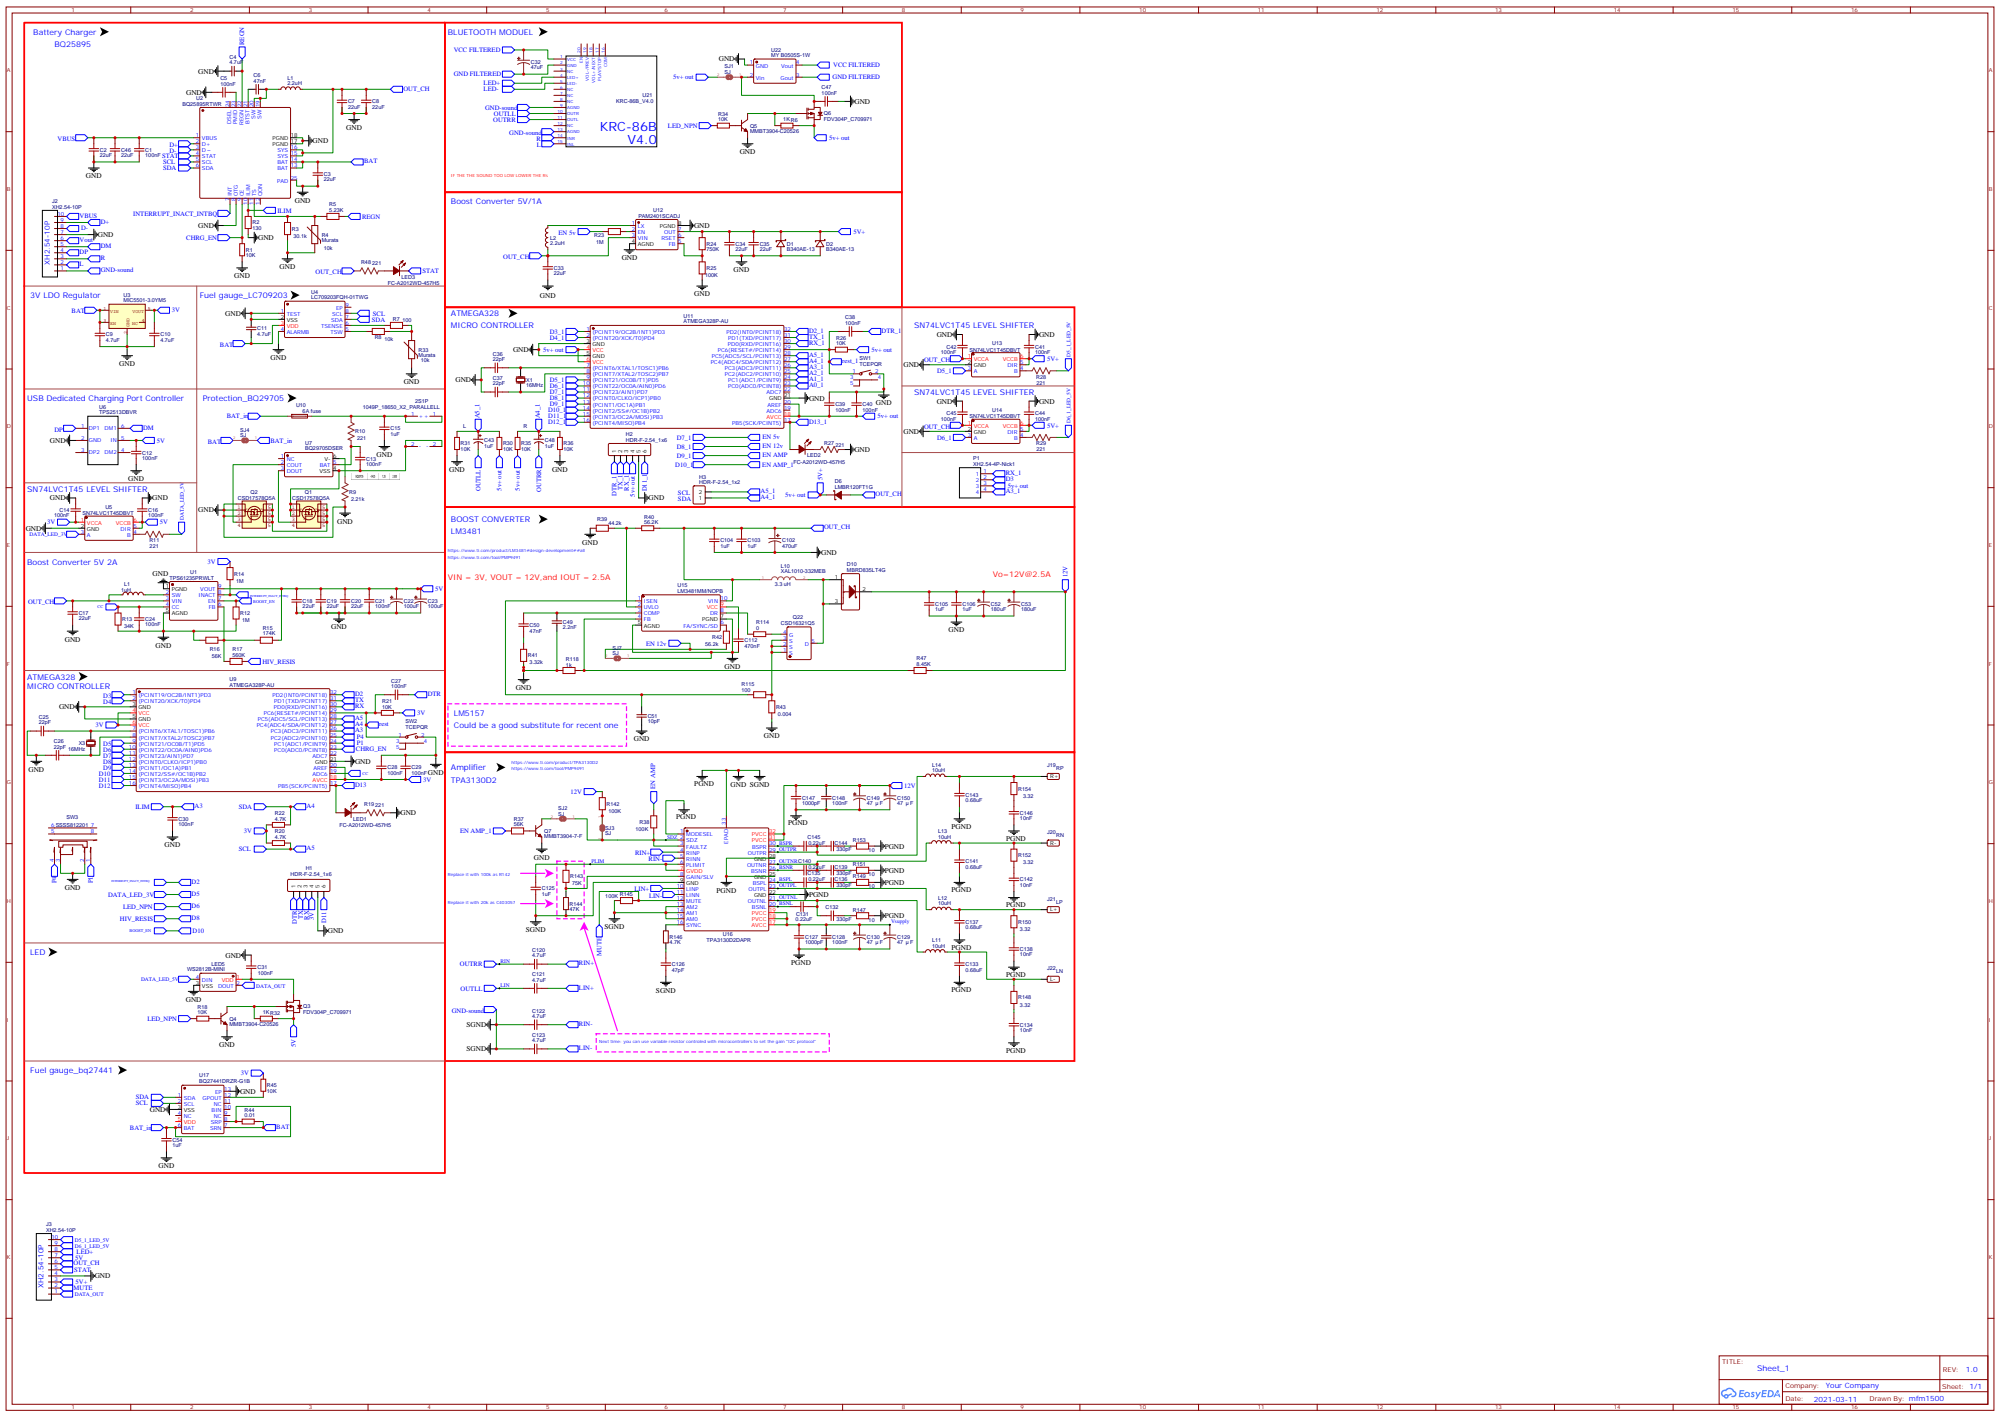
[picture p58: page 1]

BAT 13 BAT 14 SYS 15 SYS 16 PGND 17 PGND 18

IF THE THE SOUND TOO LOW LOWER THE Rs

USB Dedicated Charging Port Controller

https://www.ti.com/product/LM3481#design-development##all
https://www.ti.com/tool/PMP9491
VIN = 3V, VOUT = 12V,and IOUT = 2.5A

DTR
Could be a good substitute for recent one

https://www.ti.com/product/TPA3130D2

Replace it with 100k as R142

Replace it with 20k as C403057

Next time: you can use variable resistor controled with microcontrollers to set the gain "I2C protocol"
LIN-
