Mala2/MouDio/Prototype/Old Version/Hardware/Front/Schematic_Front _V1.pdf

## 245 SK6805_LED_Charging

## https://cms.nacsemi.com/content/AuthDatasheets/American-Opto/SMCA202PG.pdf

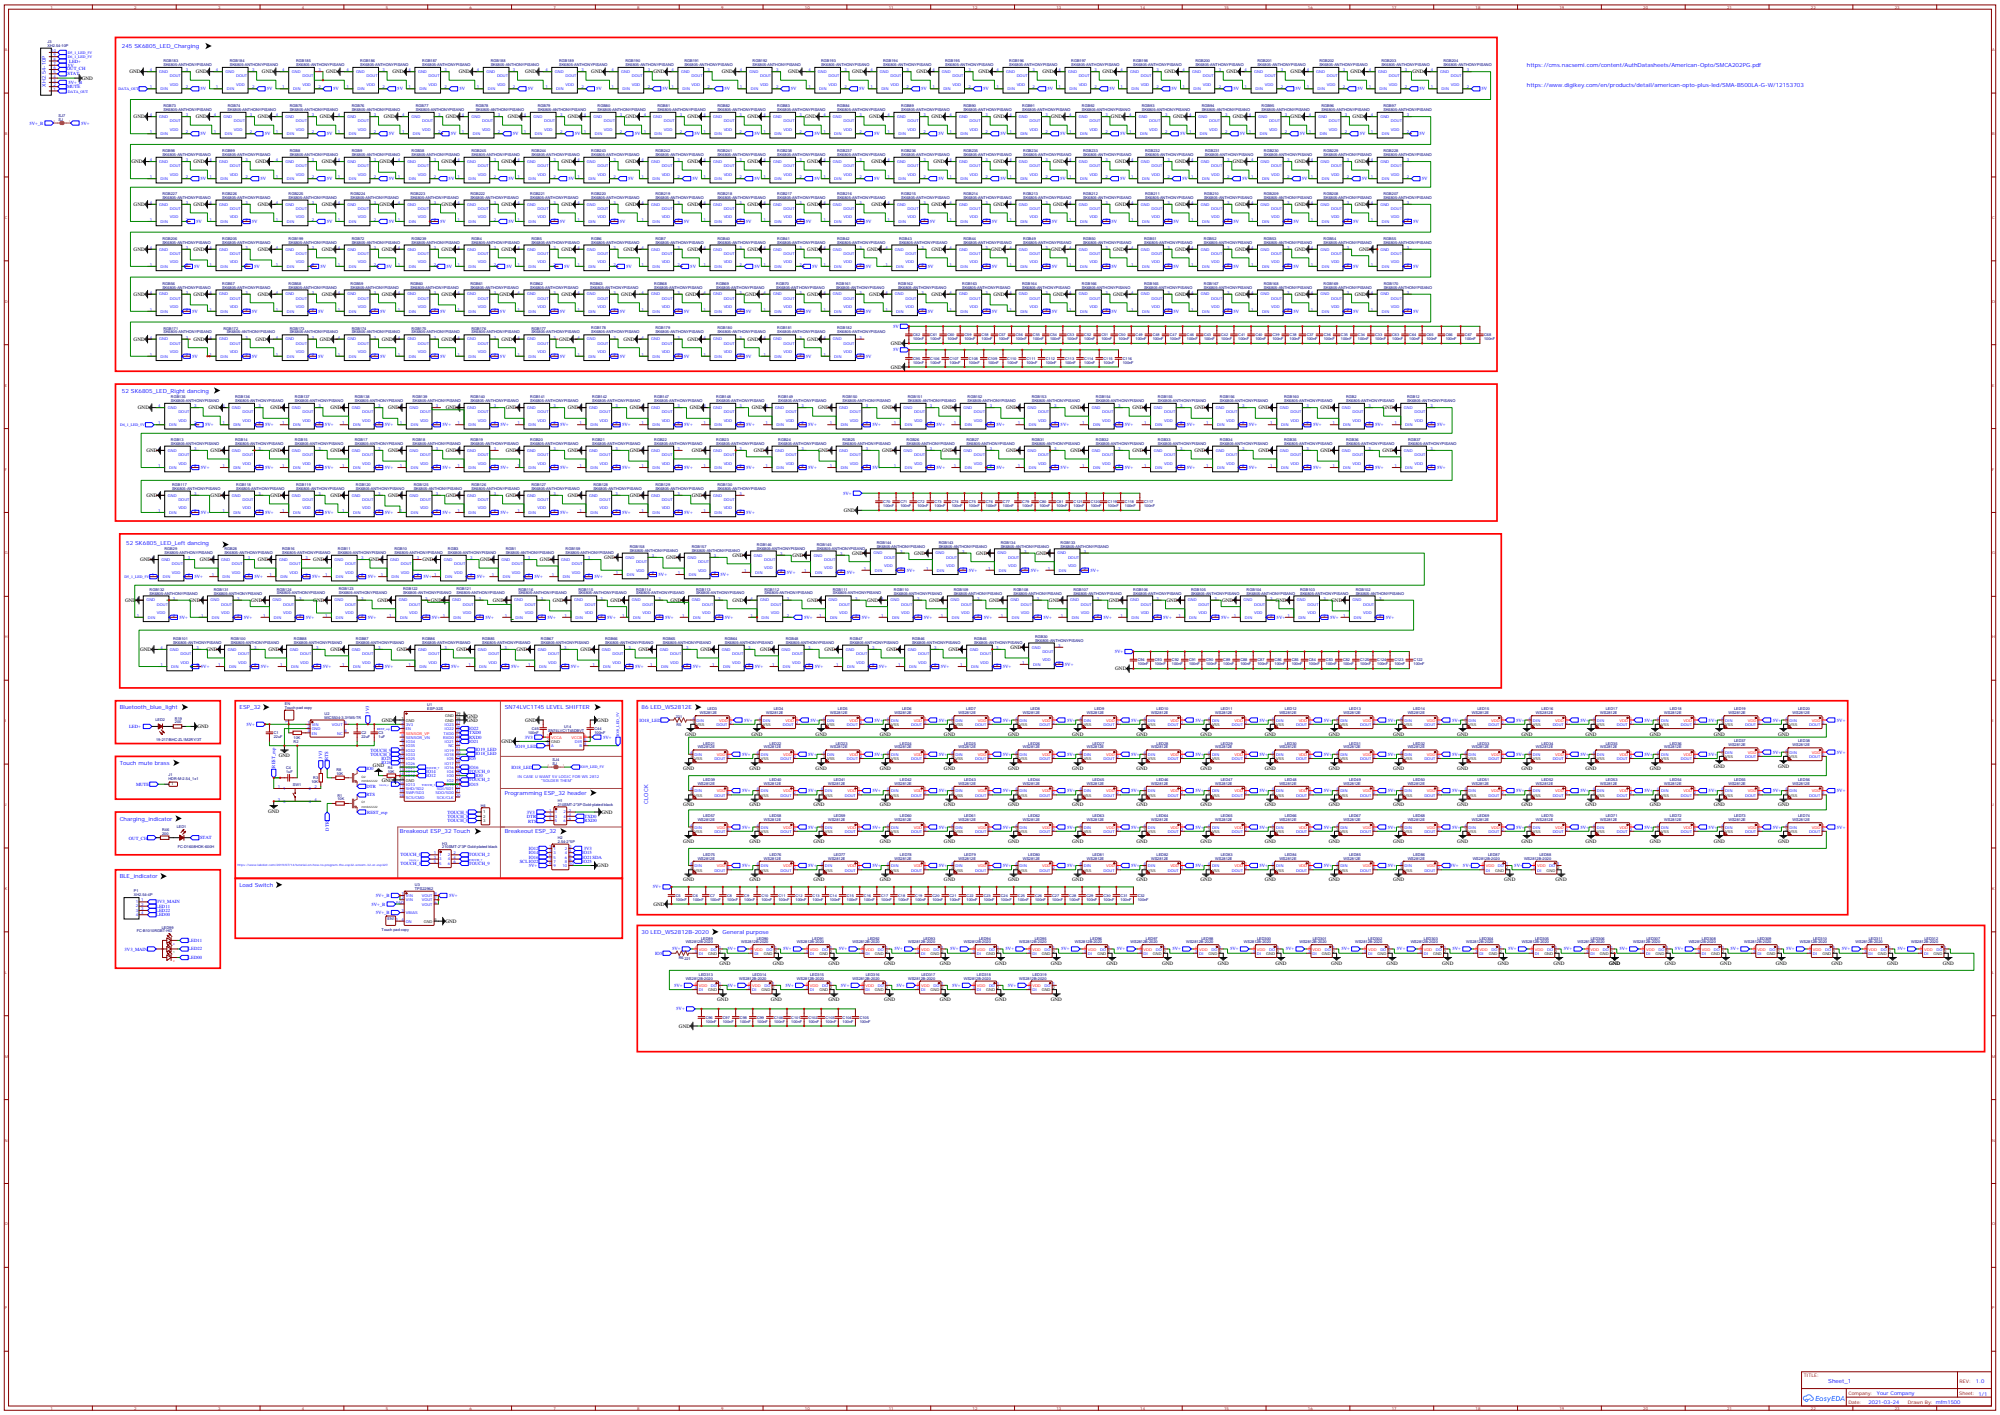
[picture p59: page 1]

https://www.digikey.com/en/products/detail/american-opto-plus-led/SMA-B500LA-G-W/12153703

IN CASE U WANT 5V LOGIC FOR WS 2812

https://www.lab4iot.com/2019/07/14/tutorial-on-how-to-program-the-esp32-wroom-32-or-esp32f/
