Mala2/MouDio/Prototype/Old Version/Hardware/USB-C/Usb-c_V1.pdf

BQ25895

## Battery Charger

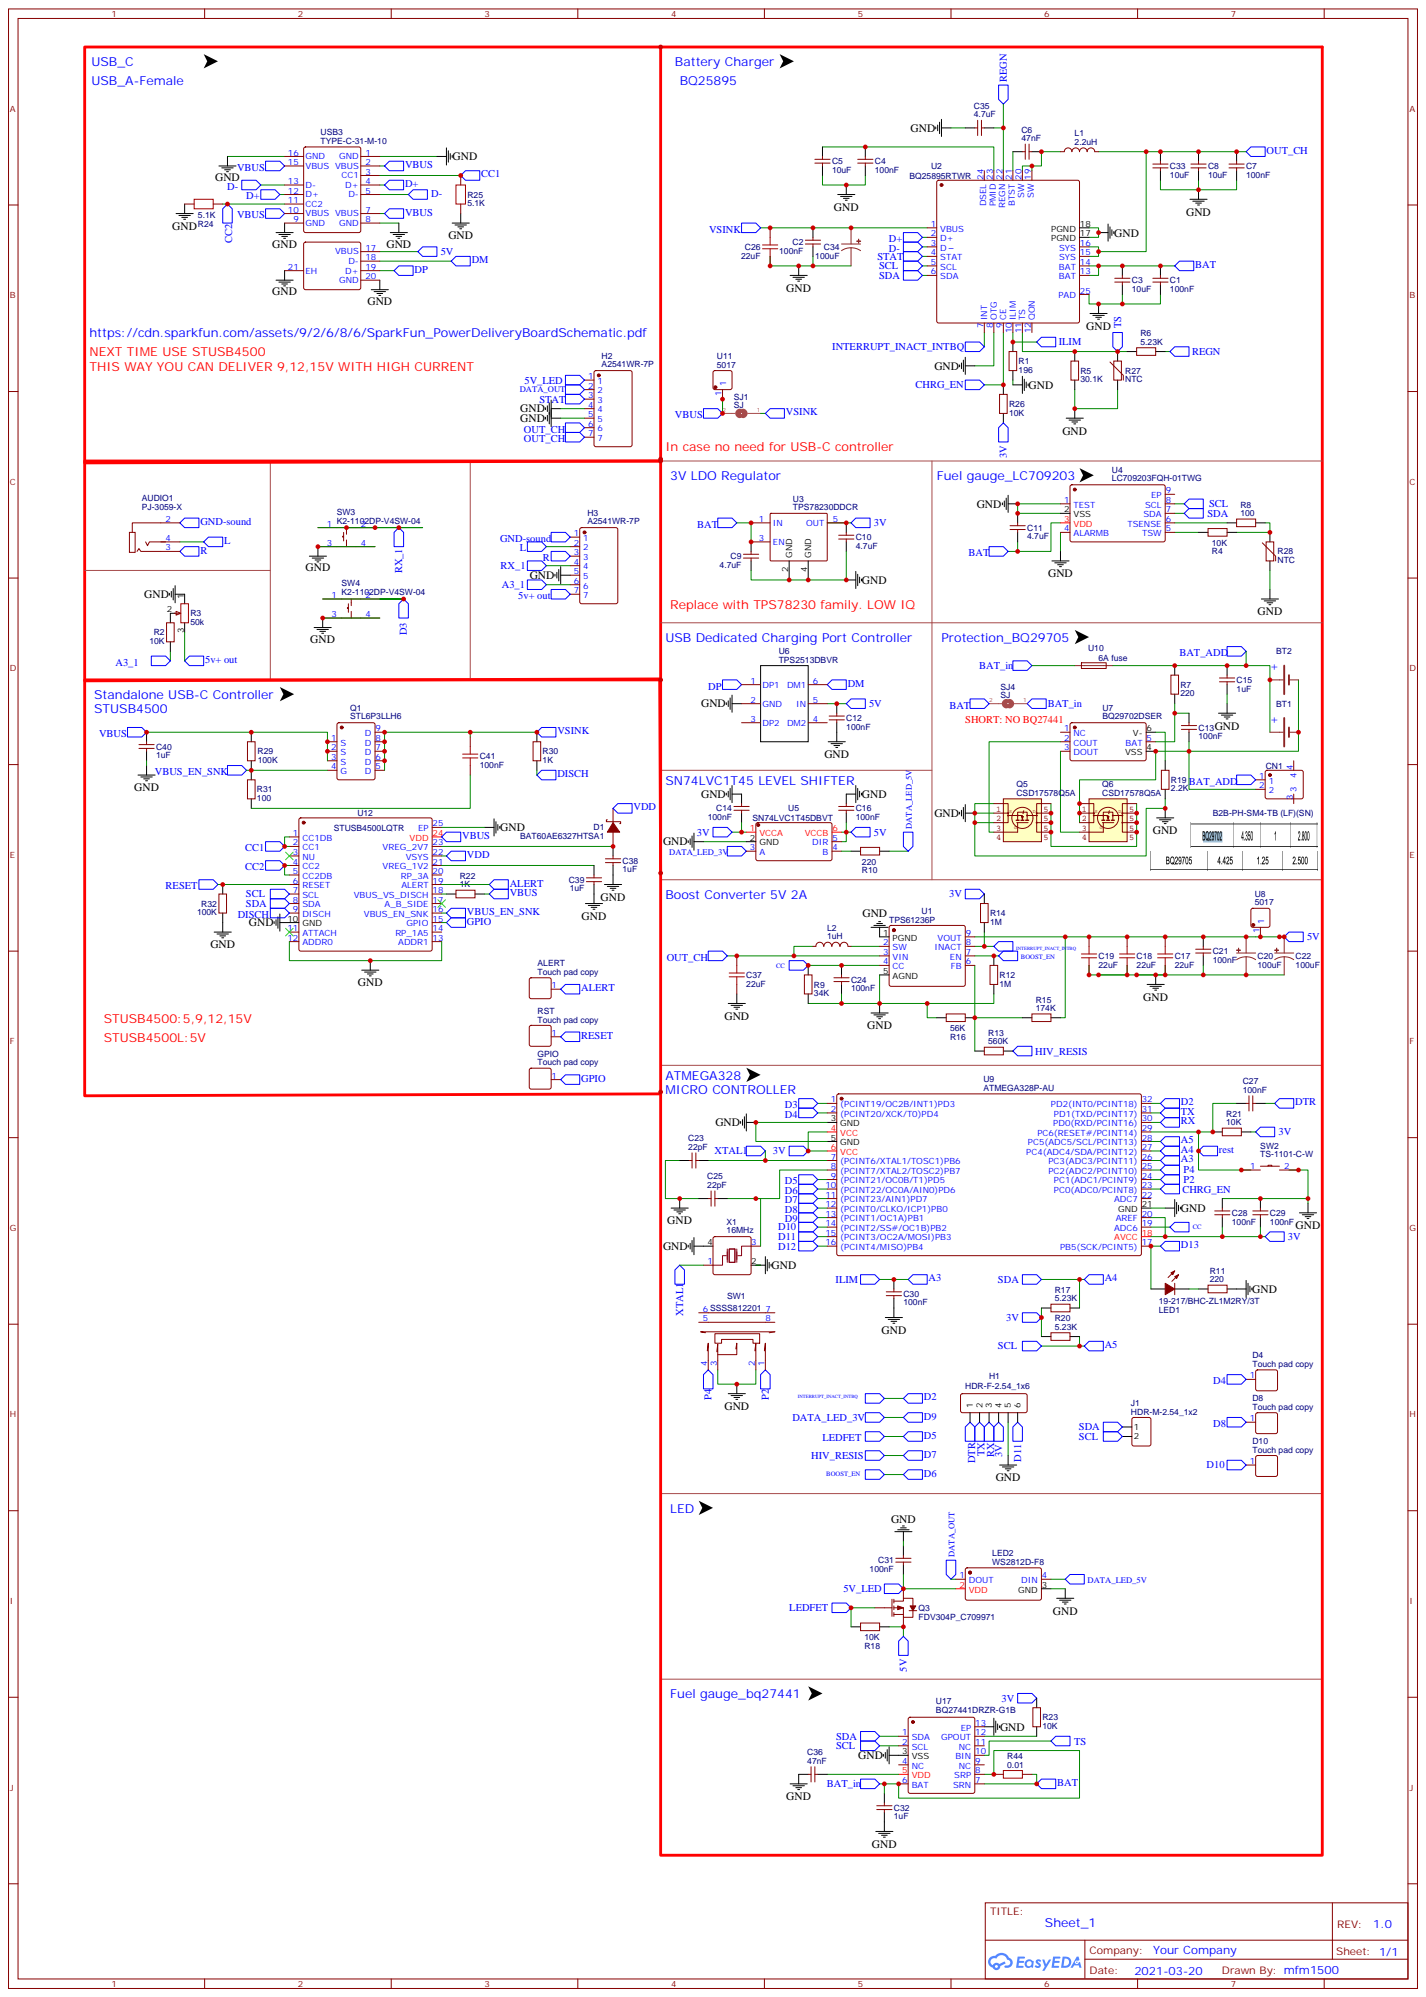
[picture p60: page 1]

https://cdn.sparkfun.com/assets/9/2/6/8/6/SparkFun_PowerDeliveryBoardSchematic.pdf
NEXT TIME USE STUSB4500
THIS WAY YOU CAN DELIVER 9,12,15V WITH HIGH CURRENT

In case no need for USB-C controller

Replace with TPS78230 family. LOW IQ

USB Dedicated Charging Port Controller
